kholia/DDX/Active-Antenna/Screenshot_2024-12-22_21-28-49.png

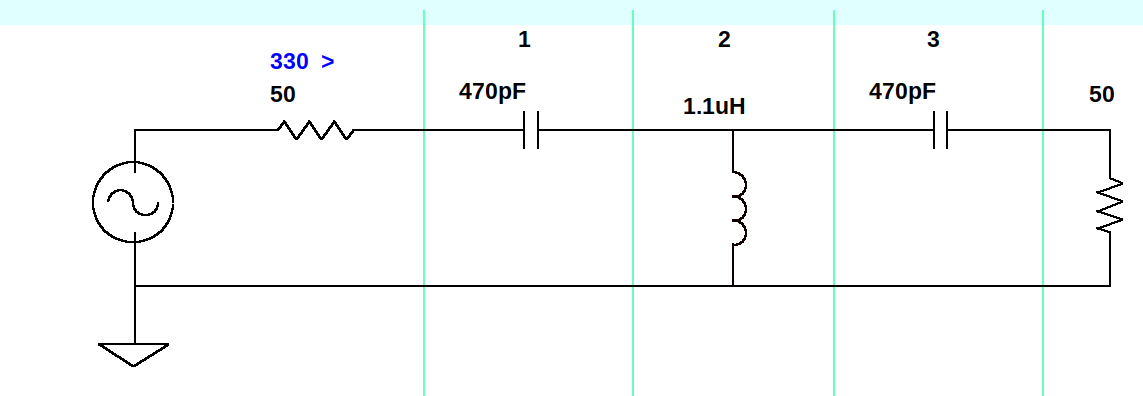
Active-Antenna/Screenshot_2024-12-22_21-28-49.png
