kholia/DDX/Active-Antenna/Screenshot_2024-12-22_21-56-25.png

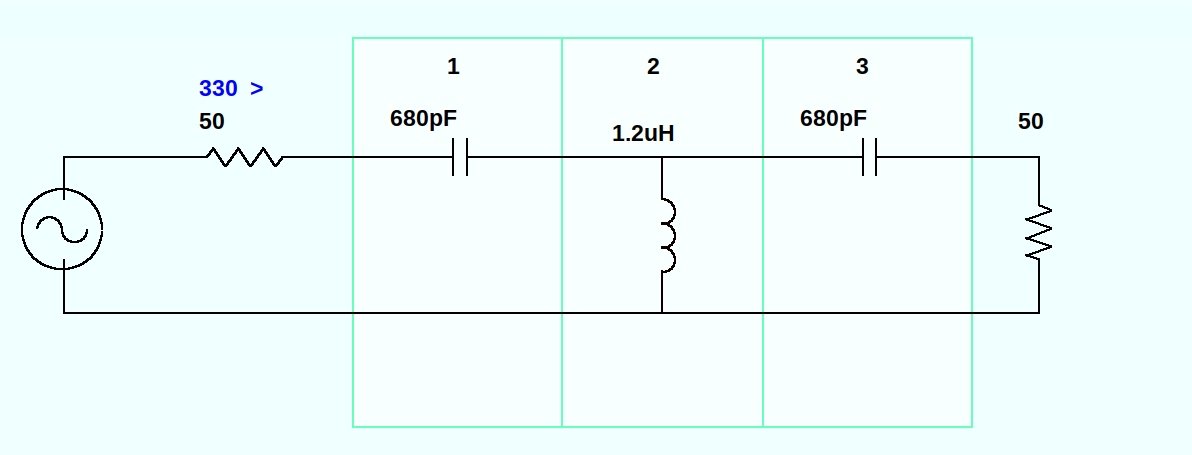
Active-Antenna/Screenshot_2024-12-22_21-56-25.png
