kholia/DDX/Active-Antenna/Screenshot_2024-12-23_18-33-32.png

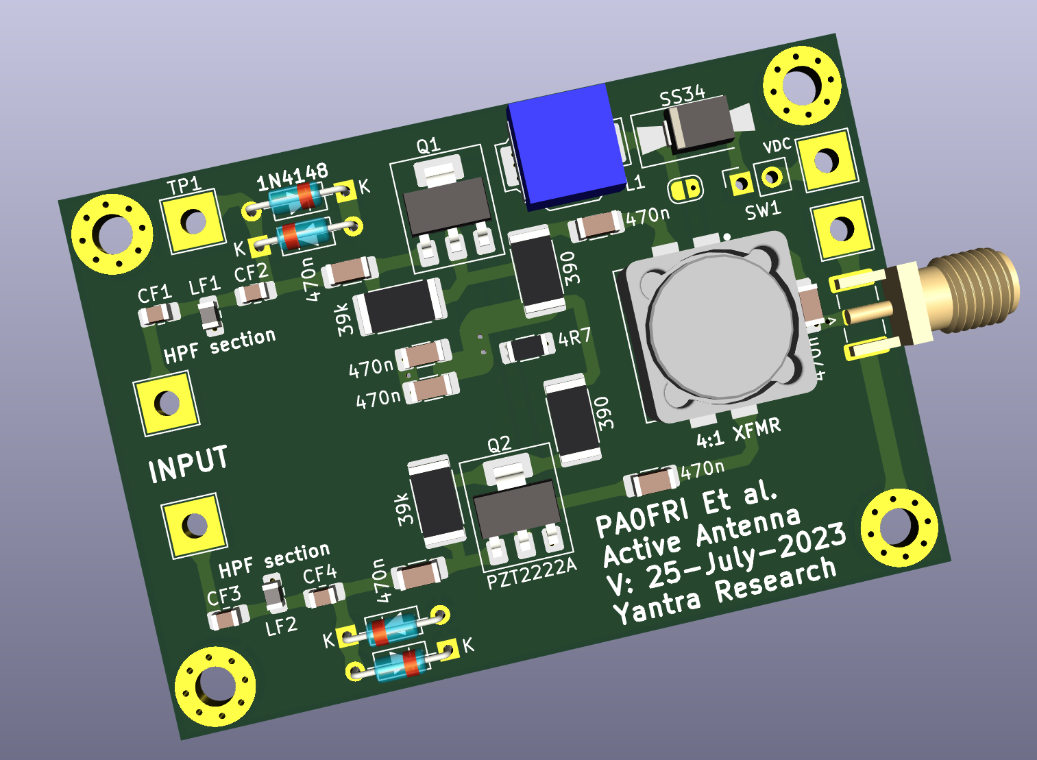
Active-Antenna/Screenshot_2024-12-23_18-33-32.png
