kholia/DDX/Active-Antenna/v 25-jul-2023.gif

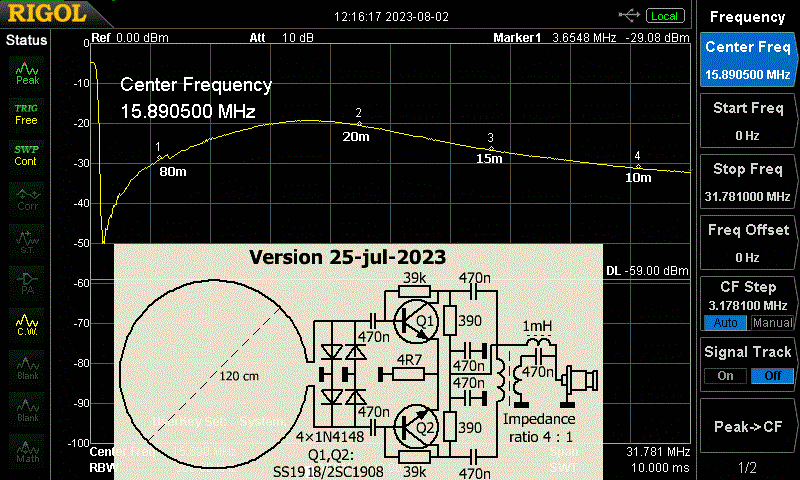
Active-Antenna/v 25-jul-2023.gif
