kholia/DDX/datasheets/8002-with-pot.jpg

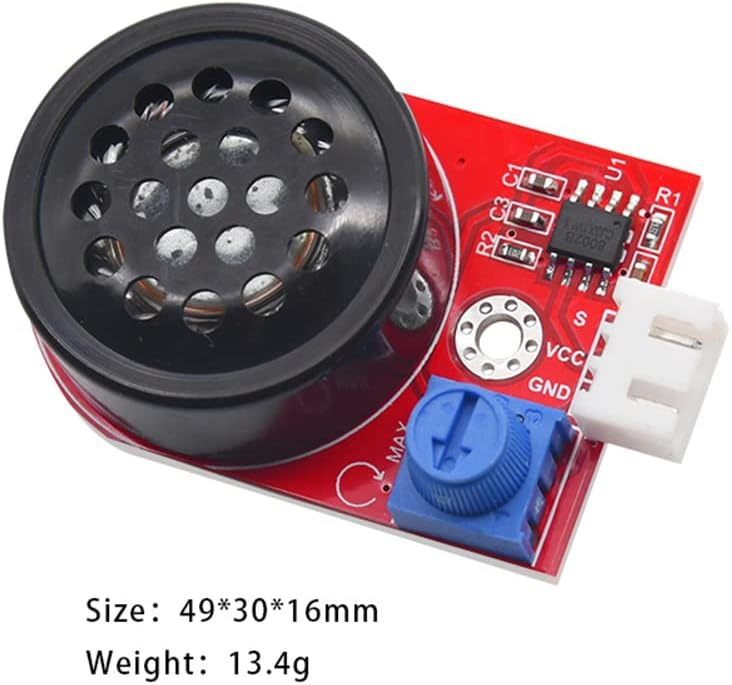
datasheets/8002-with-pot.jpg
