kholia/DDX/datasheets/CAPUF DC-DC LDO.png

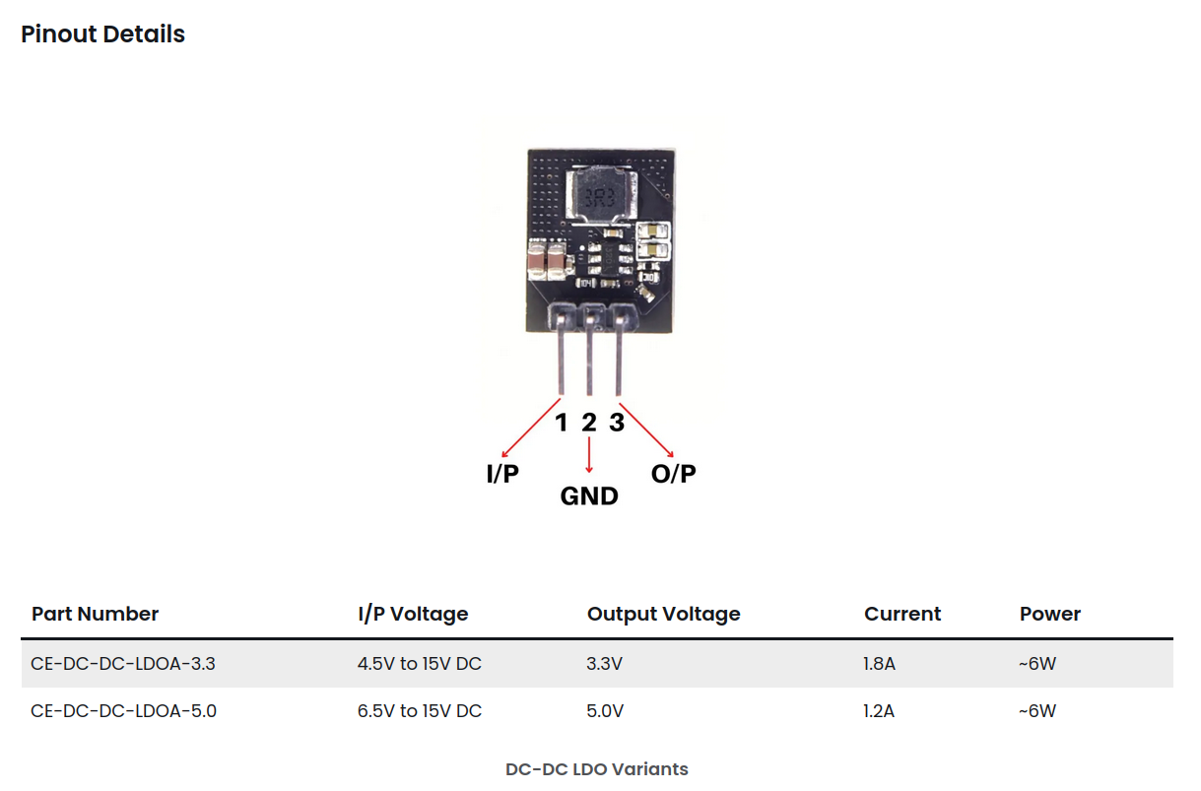
datasheets/CAPUF DC-DC LDO.png
