kholia/DDX/datasheets/Diode across relay.png

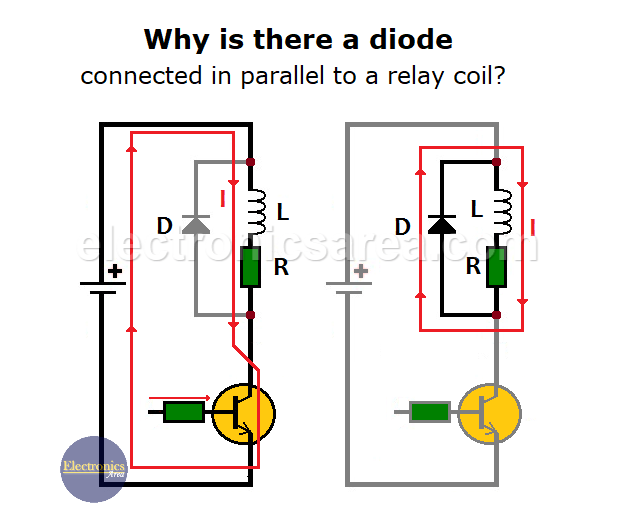
datasheets/Diode across relay.png
