kholia/DDX/datasheets/NeoPixel WS2812 LED - 5mm Diffused - THT.jpg

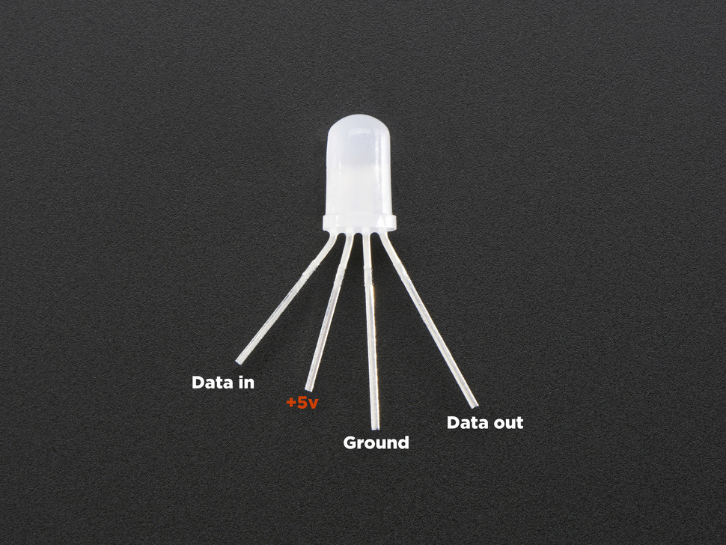
datasheets/NeoPixel WS2812 LED - 5mm Diffused - THT.jpg
