kholia/DDX/datasheets/Screenshot_2023-12-27_17-04-08.png

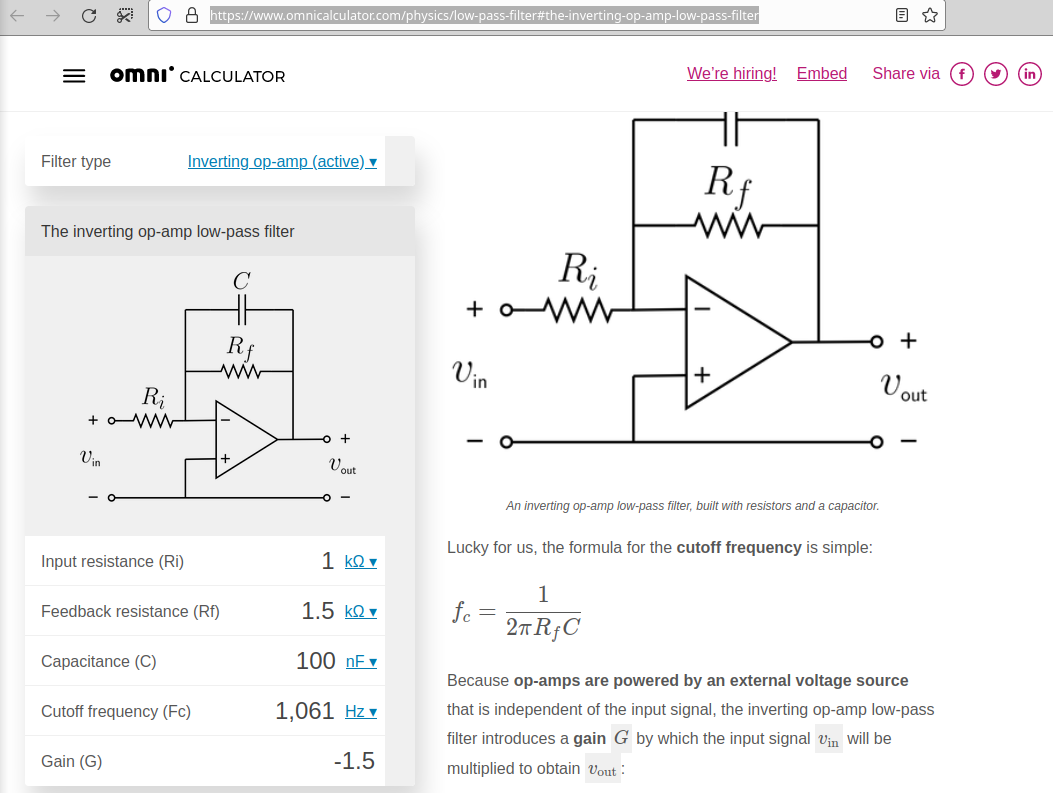
datasheets/Screenshot_2023-12-27_17-04-08.png
