kholia/DDX/datasheets/Screenshot_2024-01-10_11-48-58.png

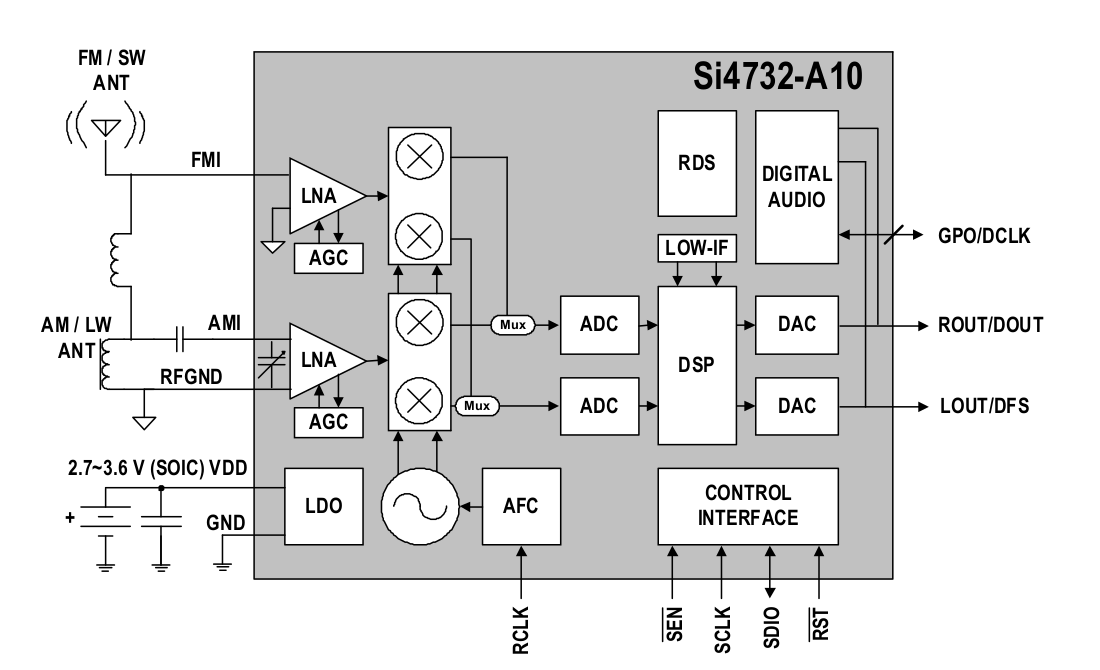
datasheets/Screenshot_2024-01-10_11-48-58.png
