kholia/DDX/datasheets/Screenshot_2024-05-21_07-38-28.png

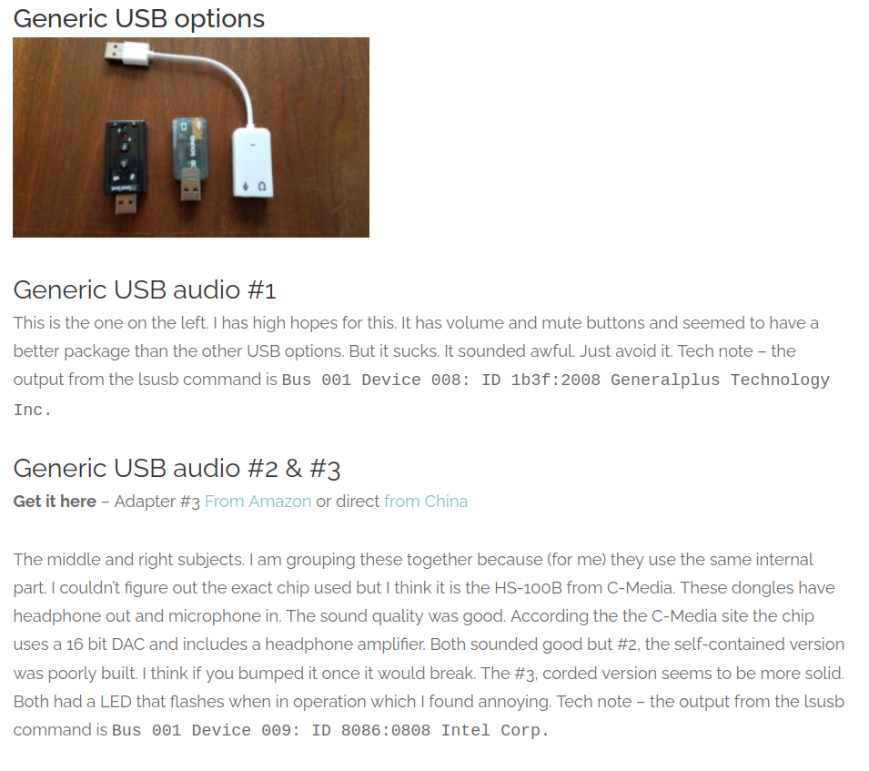
datasheets/Screenshot_2024-05-21_07-38-28.png
