kholia/DDX/datasheets/Screenshot_2024-05-21_07-54-50.png

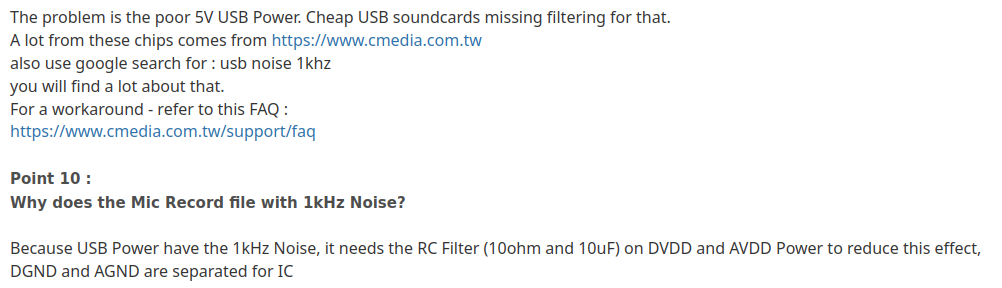
datasheets/Screenshot_2024-05-21_07-54-50.png
