kholia/DDX/datasheets/Screenshot_2024-10-01_17-50-52.png

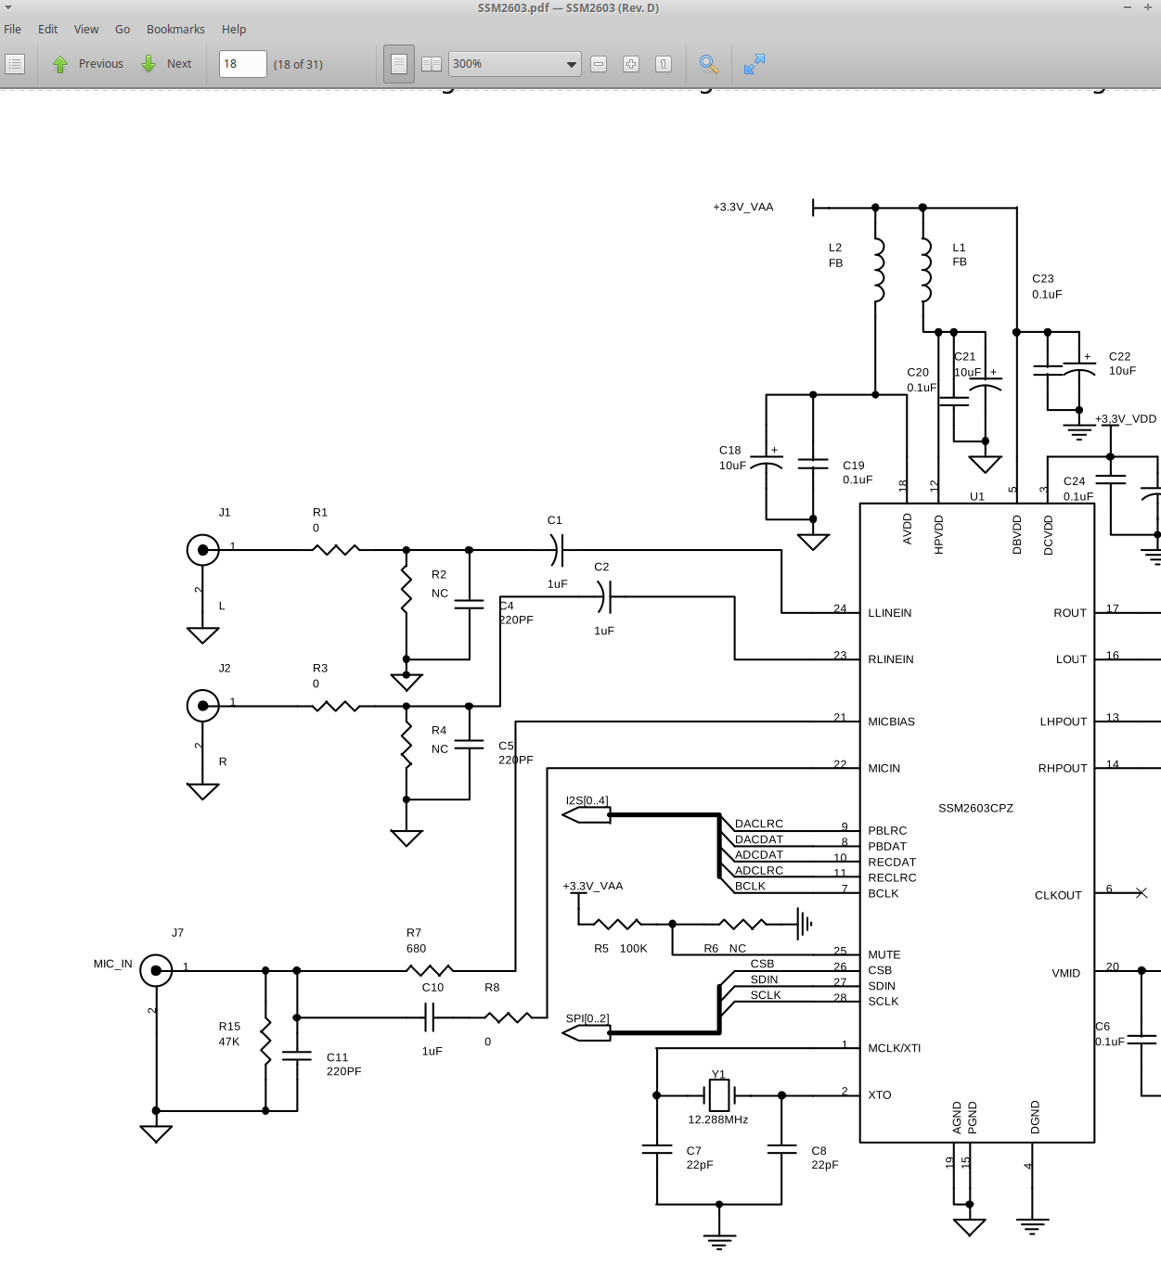
datasheets/Screenshot_2024-10-01_17-50-52.png
