kholia/DDX/datasheets/Screenshot_2024-10-03_21-19-48.png

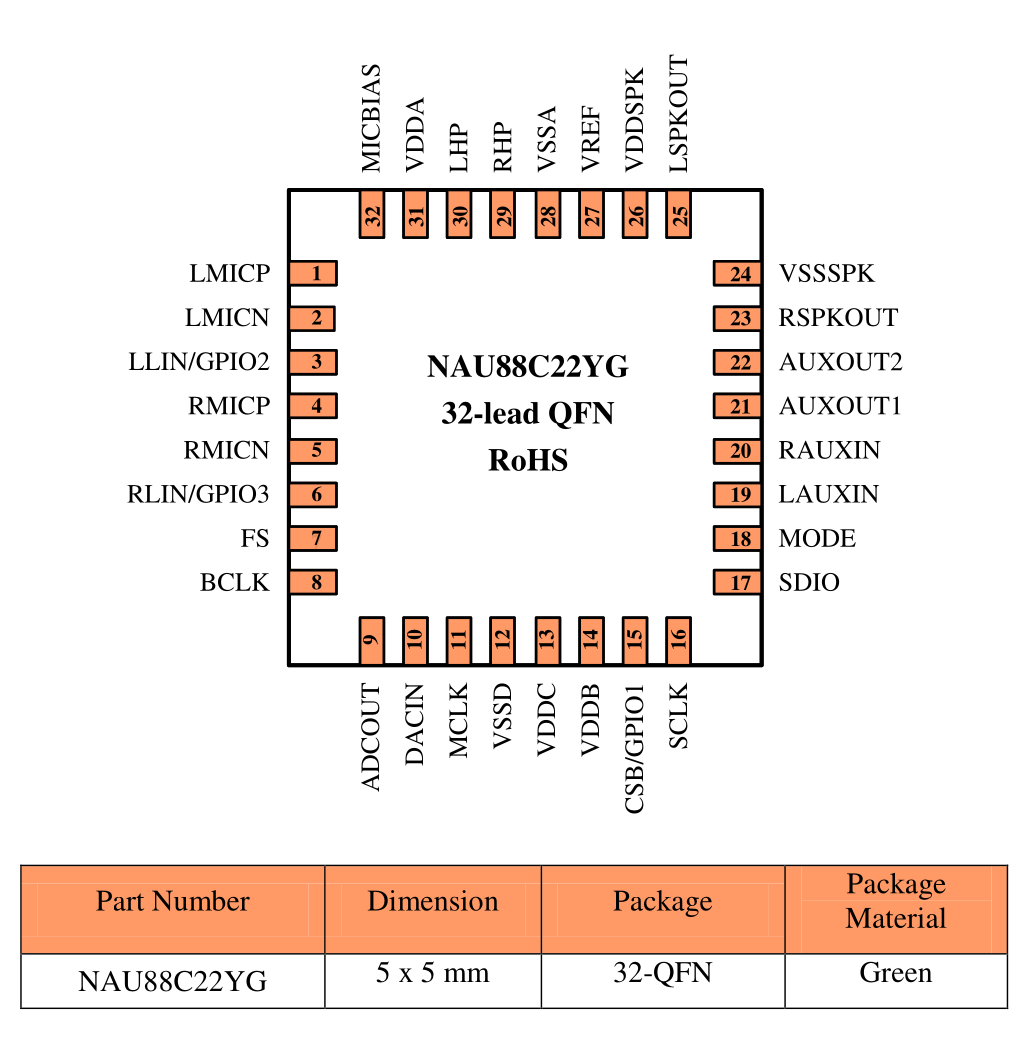
datasheets/Screenshot_2024-10-03_21-19-48.png
