kholia/DDX/datasheets/Screenshot_2024-10-03_21-23-47.png

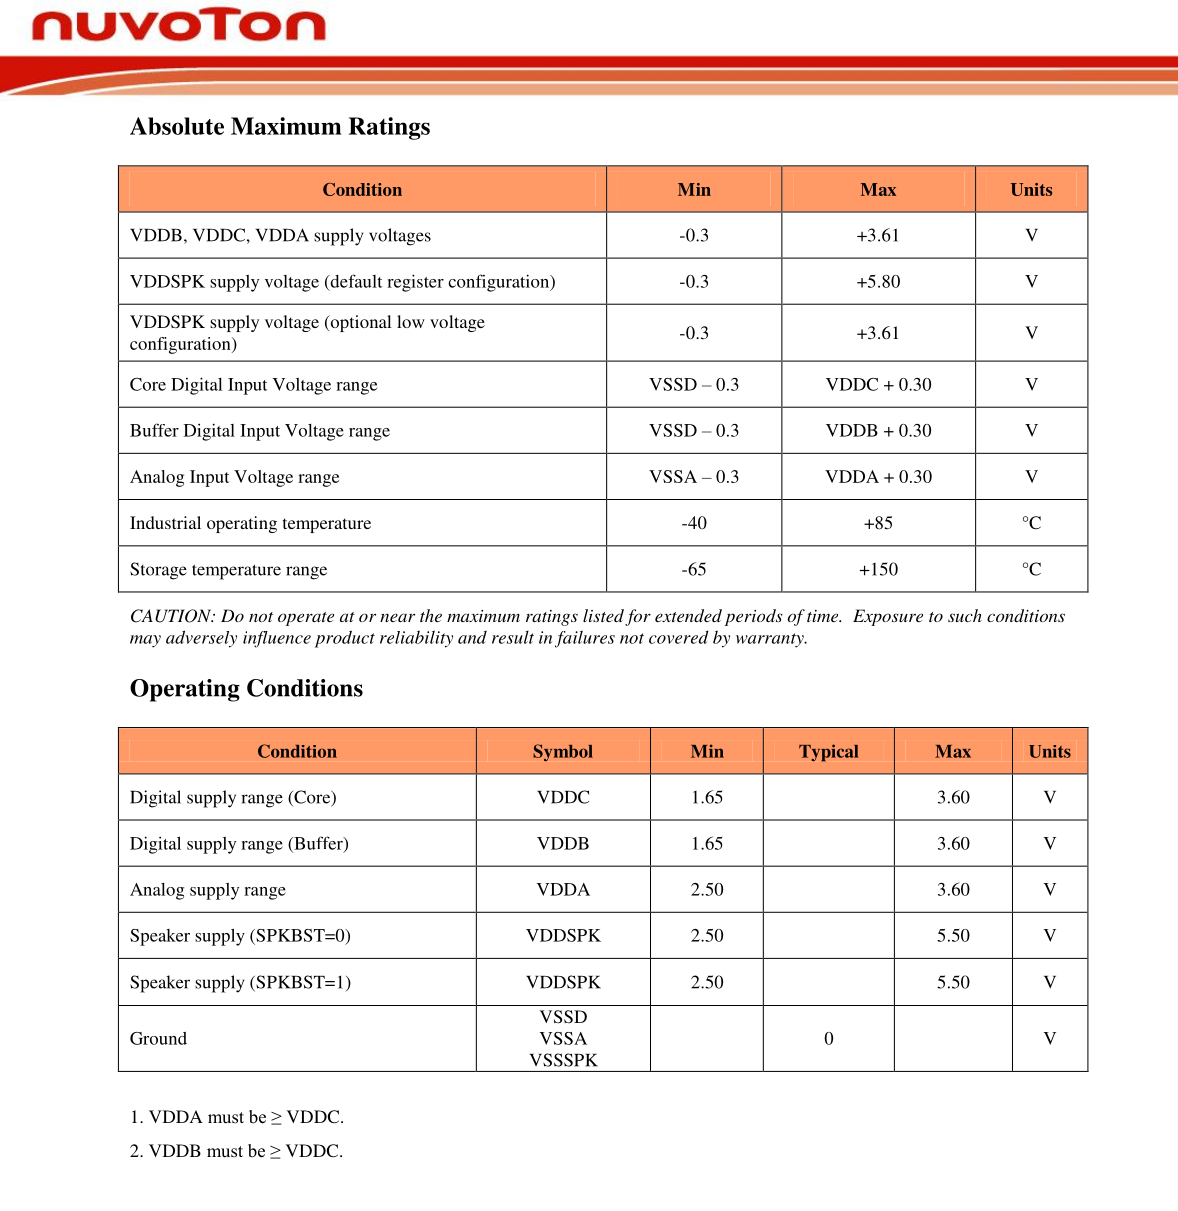
datasheets/Screenshot_2024-10-03_21-23-47.png
