kholia/DDX/datasheets/SFU455B Pinout.png

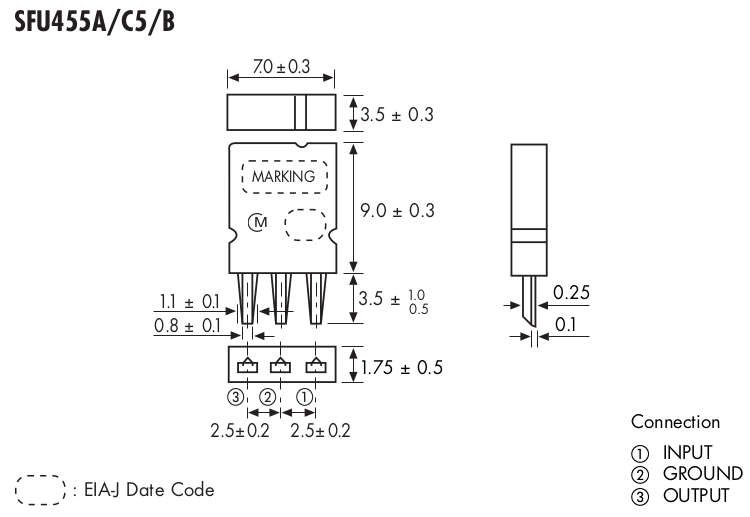
datasheets/SFU455B Pinout.png
