kholia/DDX/datasheets/speaker-for-micro-bit-1-500x500.jpg

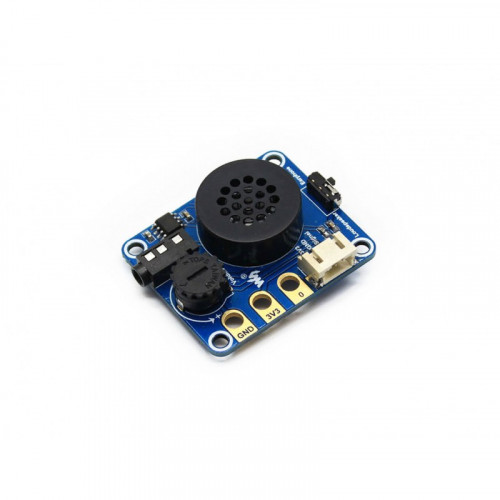
datasheets/speaker-for-micro-bit-1-500x500.jpg
