kholia/DDX/DDX-1-R1.10/3D-Render.png

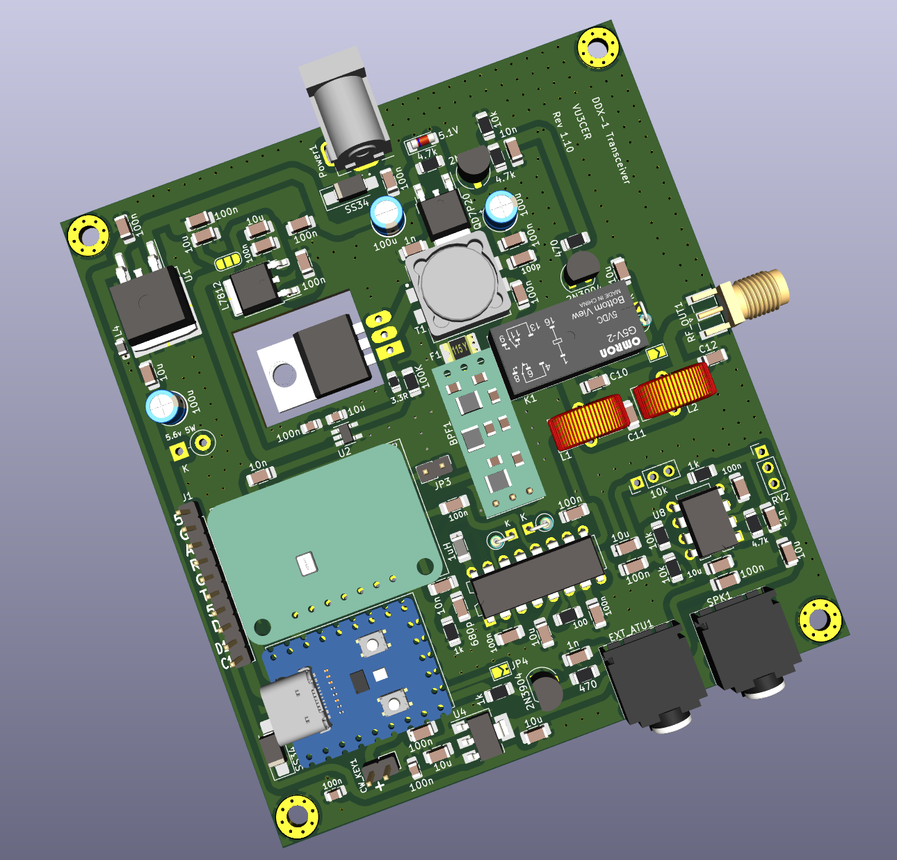
DDX-1-R1.10/3D-Render.png
