kholia/DDX/DDX-1-R1.10/Screenshot_2023-11-16_10-58-44.png

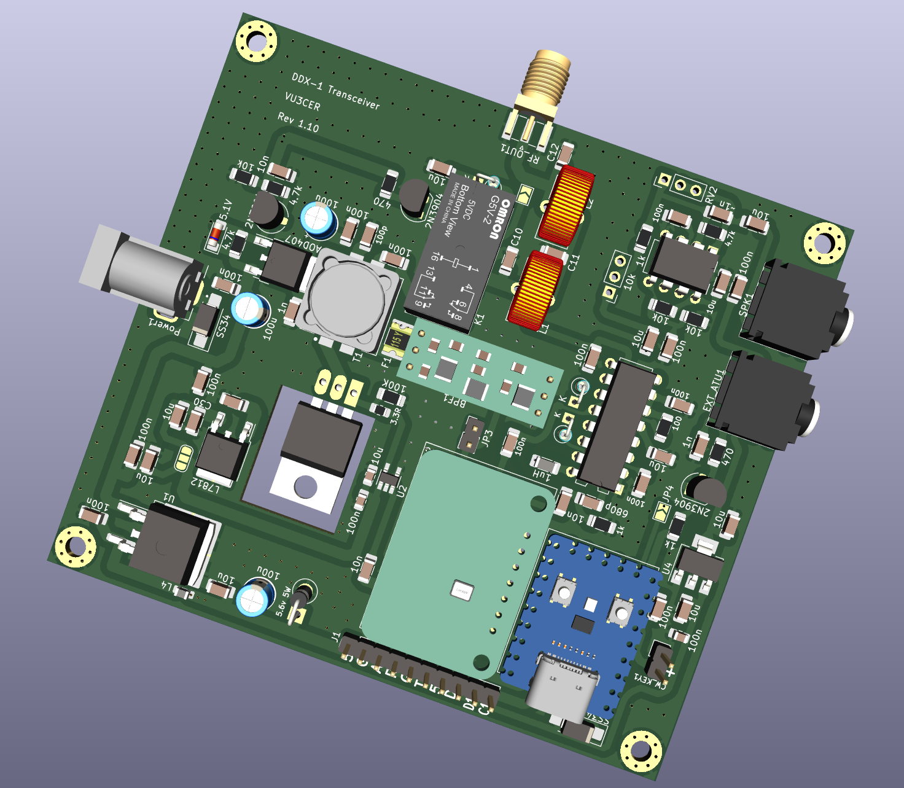
DDX-1-R1.10/Screenshot_2023-11-16_10-58-44.png
