kholia/DDX/DDX-1-R1.10/Screenshot_2024-07-12_11-12-55.png

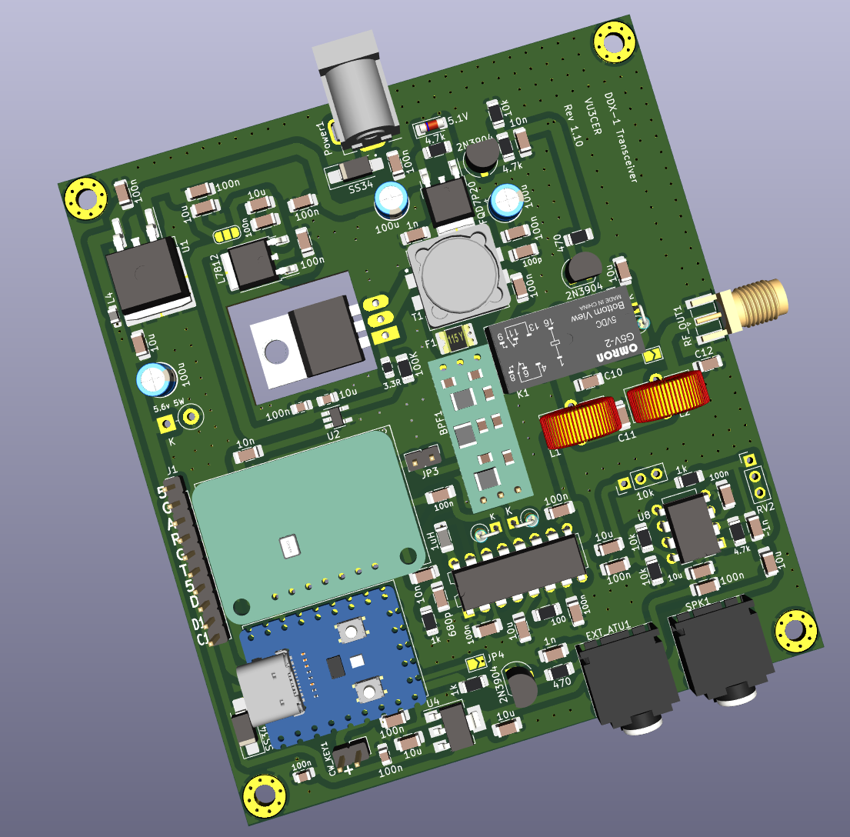
DDX-1-R1.10/Screenshot_2024-07-12_11-12-55.png
