kholia/DDX/Pictures/IMG_20231203_173641.jpg

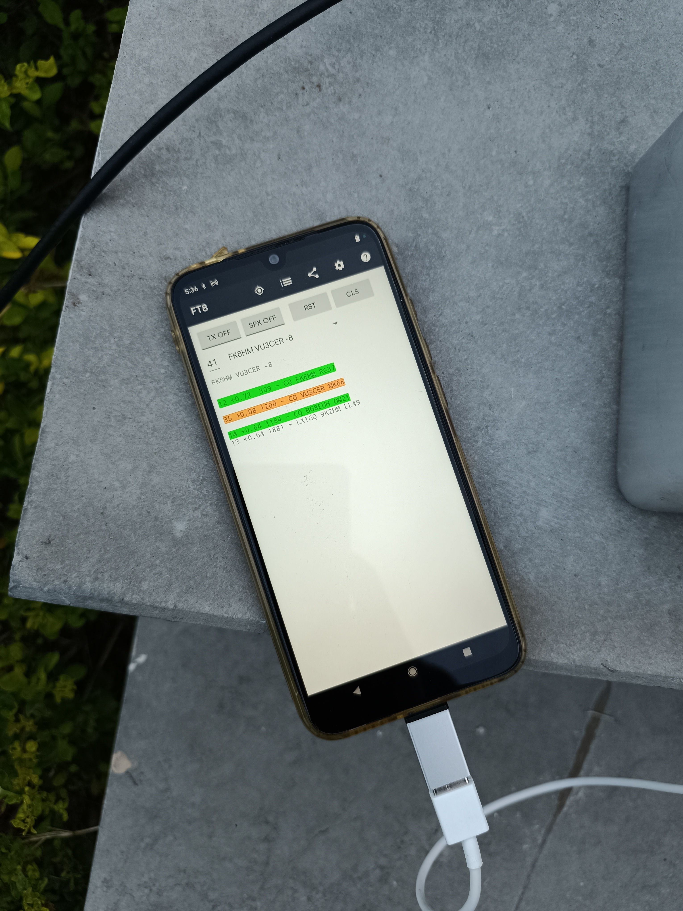
Pictures/IMG_20231203_173641.jpg
