kholia/DDX/Pictures/IMG_20231222_163501.jpg

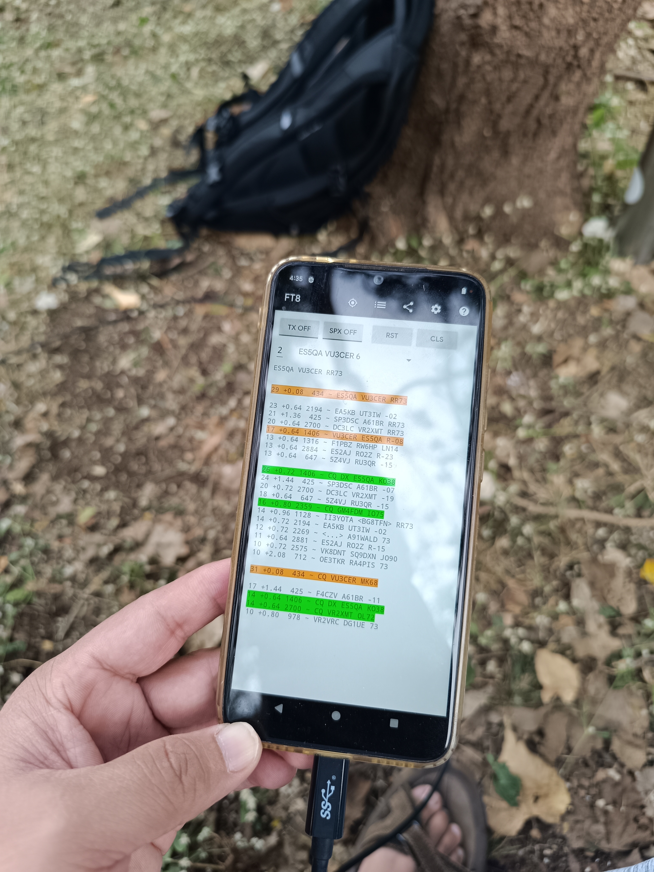
Pictures/IMG_20231222_163501.jpg
