kholia/DDX/Pictures/IMG_20231222_163504.jpg

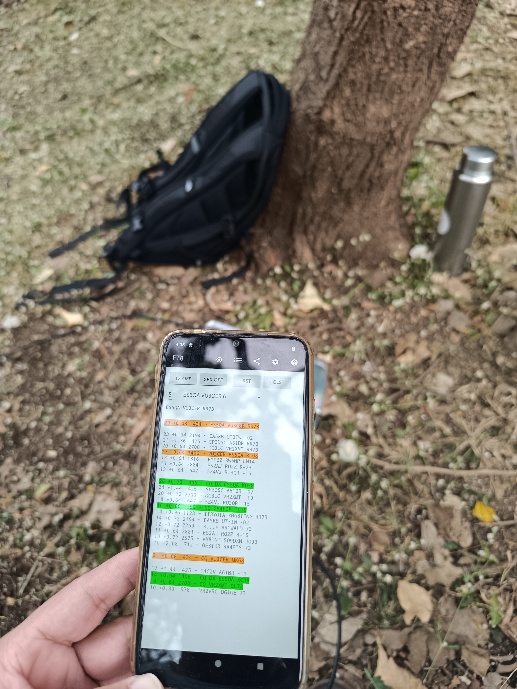
Pictures/IMG_20231222_163504.jpg
