kholia/DDX/Pictures/IMG_20231225_163345.jpg

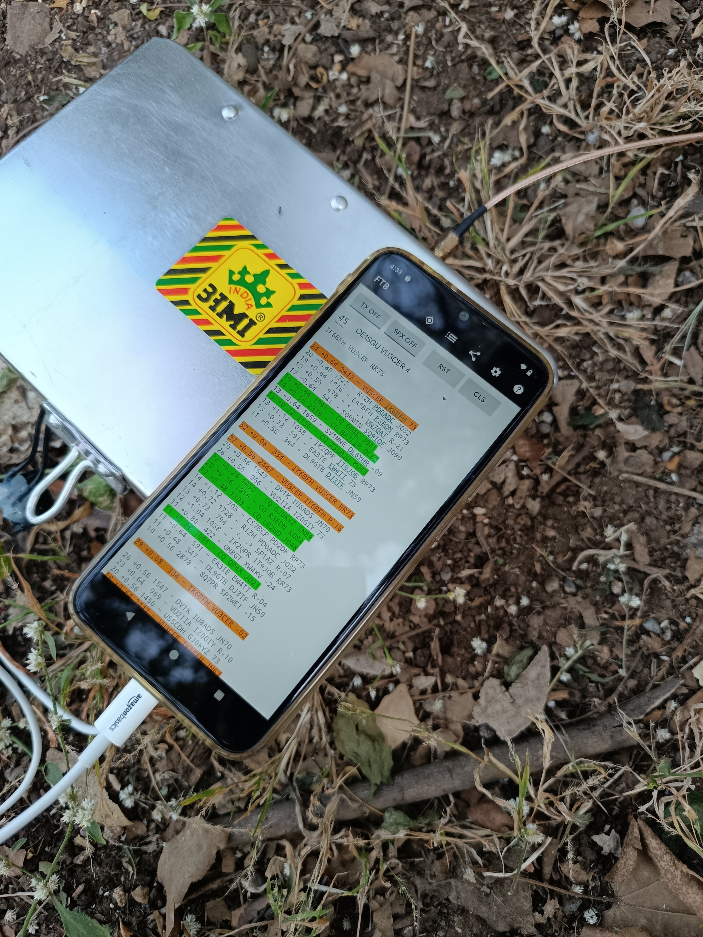
Pictures/IMG_20231225_163345.jpg
