kholia/DDX/Pictures/IMG_20231225_171434.jpg

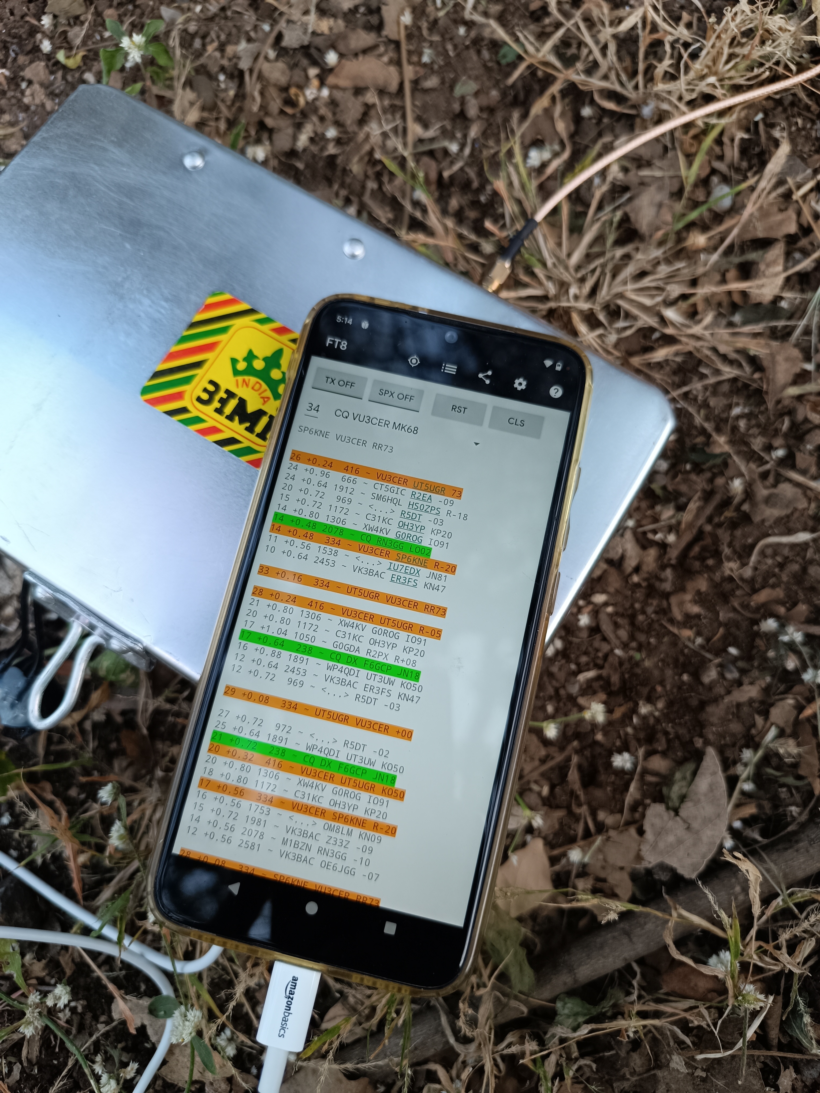
Pictures/IMG_20231225_171434.jpg
