kholia/DDX/Pictures/picture_reduced.png

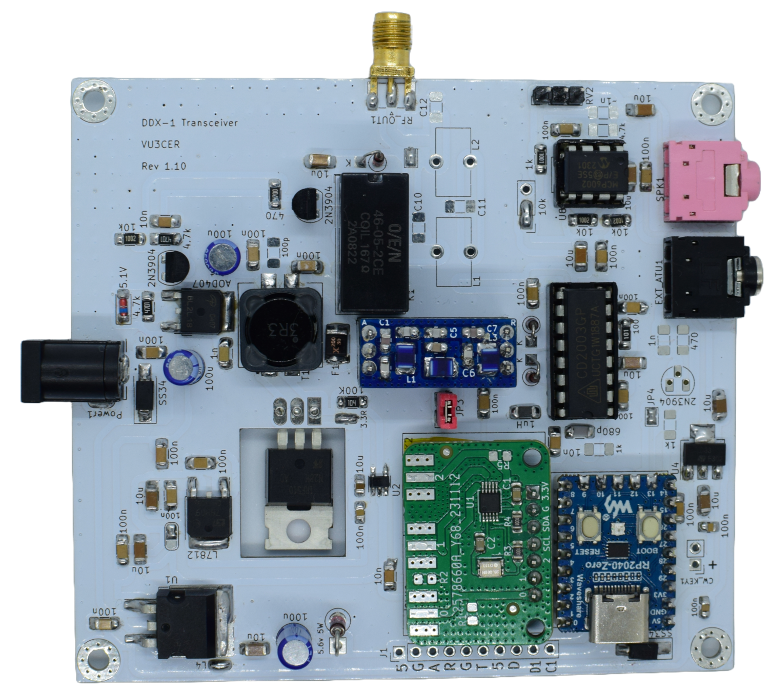
Pictures/picture_reduced.png
