kholia/DDX/Pictures/smaller_with_hs.png

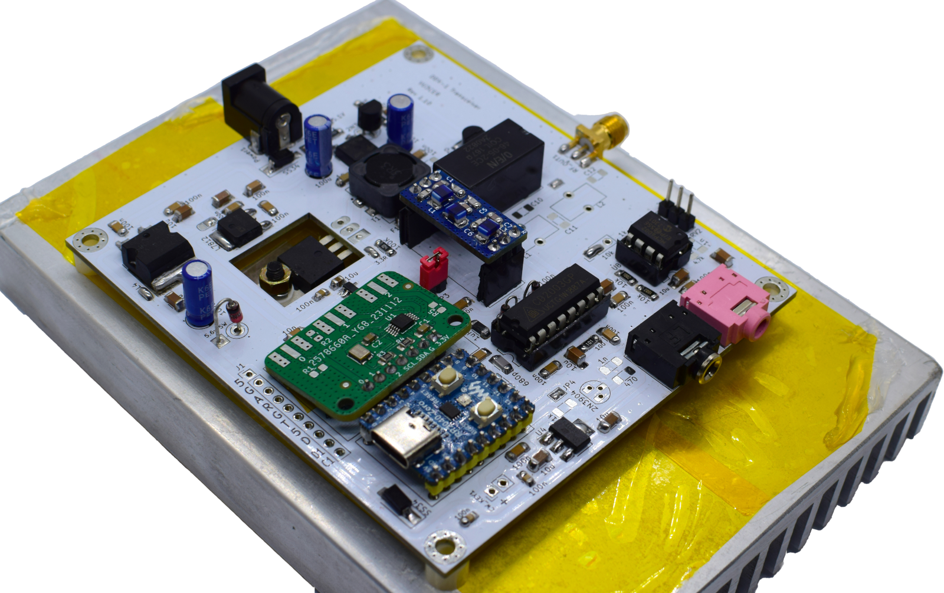
Pictures/smaller_with_hs.png
