kholia/DDX/RX-TX-BPF-2025-v2/14M-Screenshot_2024-12-20_16-44-34.png

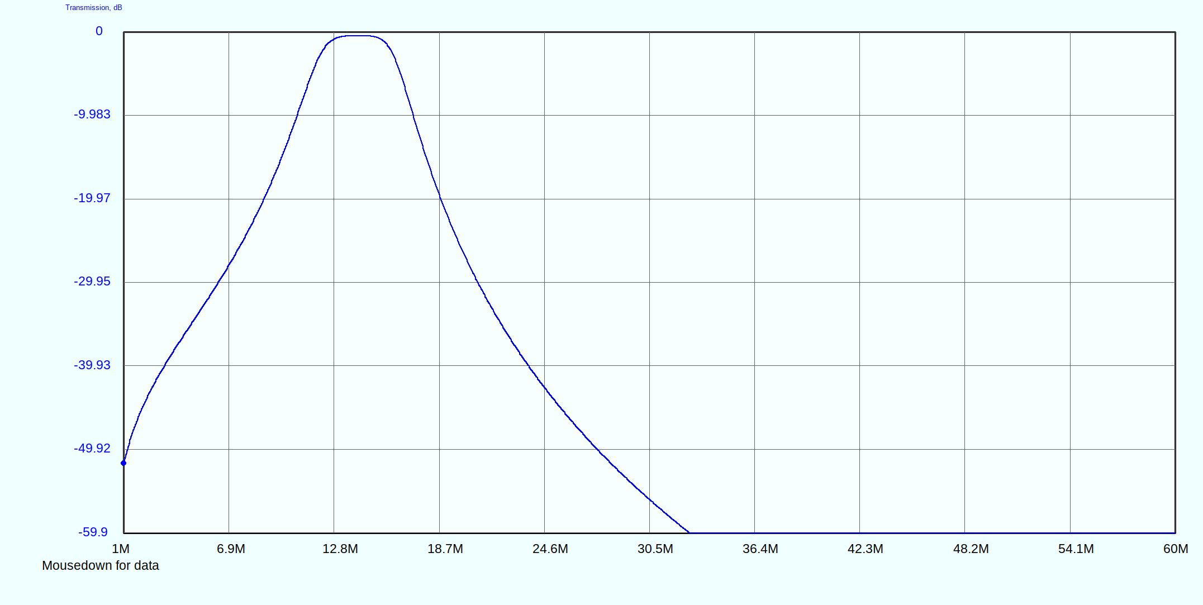
RX-TX-BPF-2025-v2/14M-Screenshot_2024-12-20_16-44-34.png
