kholia/DDX/RX-TX-BPF-2025-v2/28M-Screenshot_2024-12-19_19-49-46.png

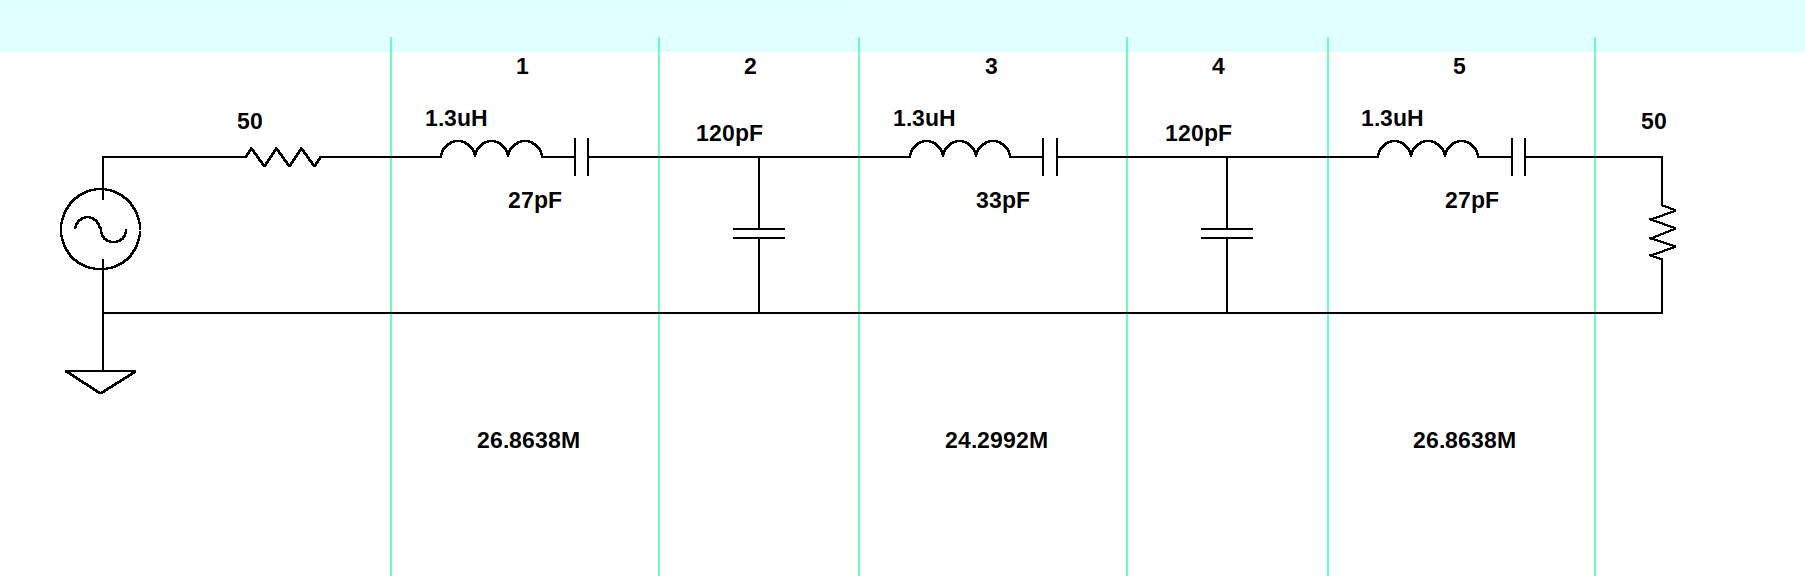
RX-TX-BPF-2025-v2/28M-Screenshot_2024-12-19_19-49-46.png
