kholia/DDX/RX-TX-BPF-2025-v2/Modeling-Actual-Values-28-MHz/Screenshot_2024-12-20_11-46-58.png

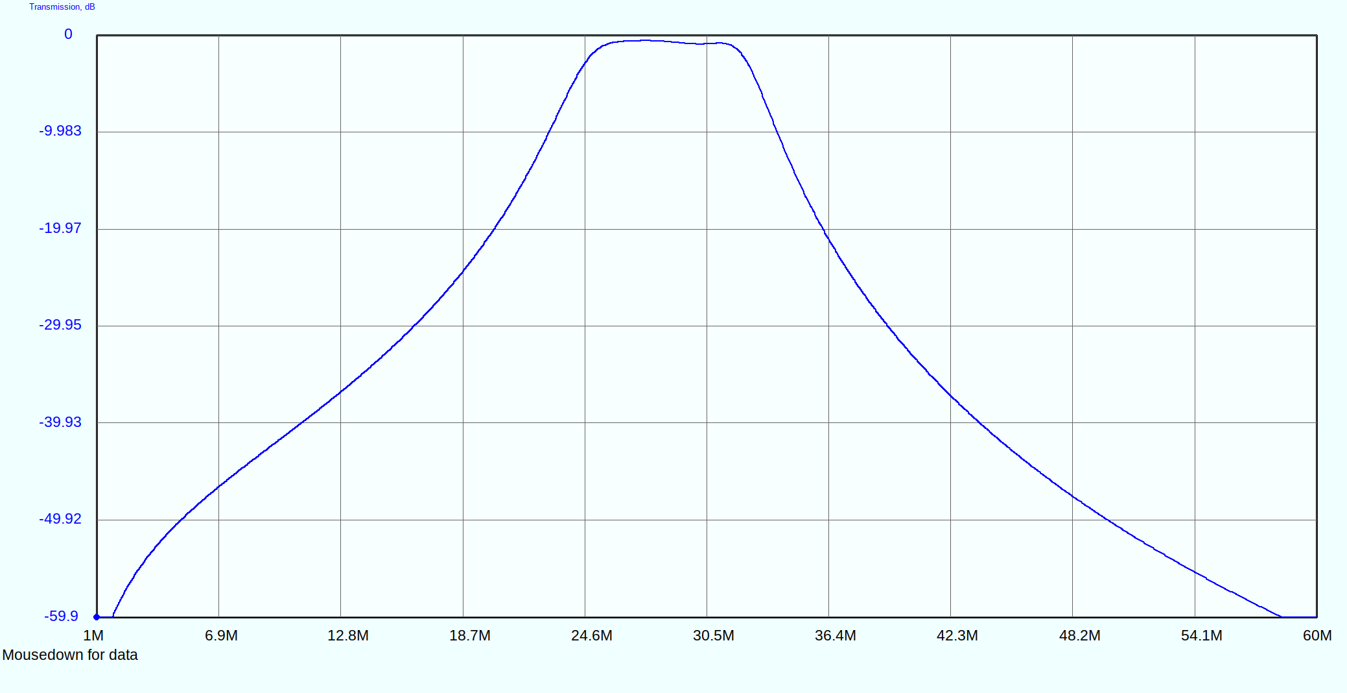
RX-TX-BPF-2025-v2/Modeling-Actual-Values-28-MHz/Screenshot_2024-12-20_11-46-58.png
