kholia/DDX/RX-TX-BPF-2025-v2/pft-practical.png

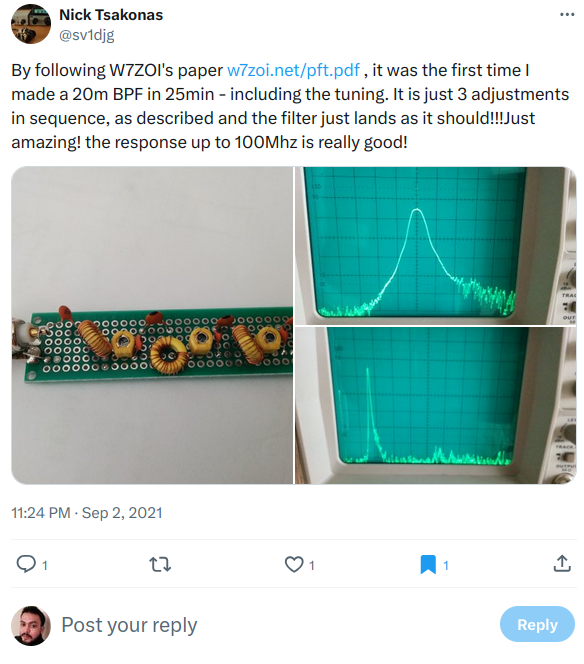
RX-TX-BPF-2025-v2/pft-practical.png
