kholia/DDX/RX-TX-BPF-2025-v2/Screenshot_2024-12-20_12-20-08.png

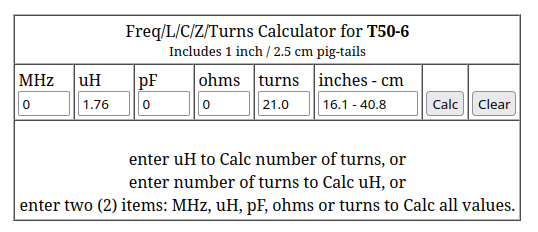
RX-TX-BPF-2025-v2/Screenshot_2024-12-20_12-20-08.png
