kholia/DDX/RX-TX-BPF-2025-v2/Screenshot_2024-12-23_11-25-25.png

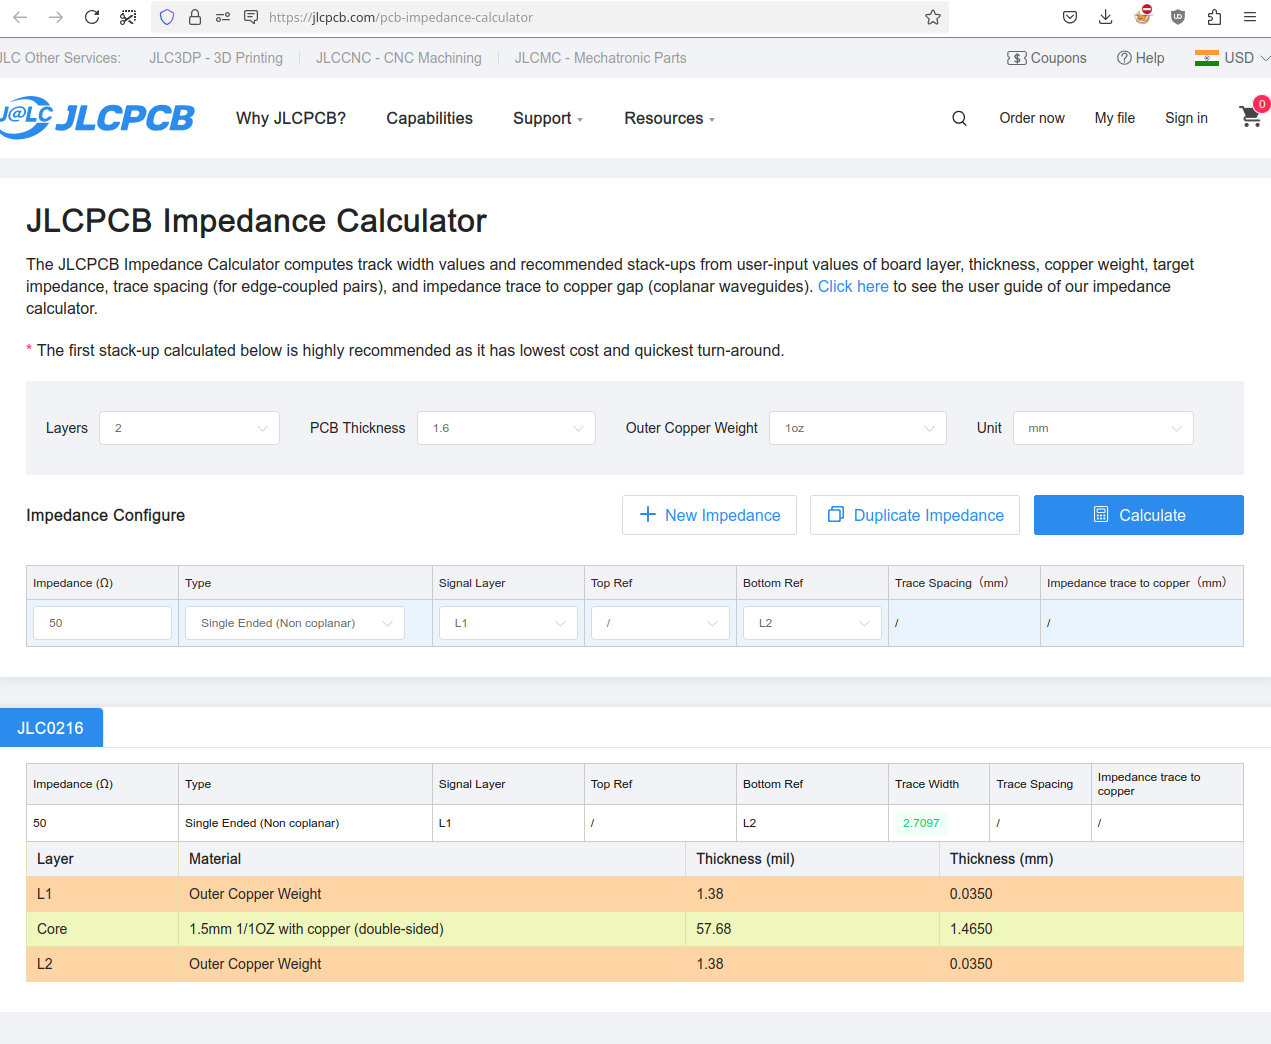
RX-TX-BPF-2025-v2/Screenshot_2024-12-23_11-25-25.png
