kholia/DDX/screenshots/DDX-Commercial-3.png

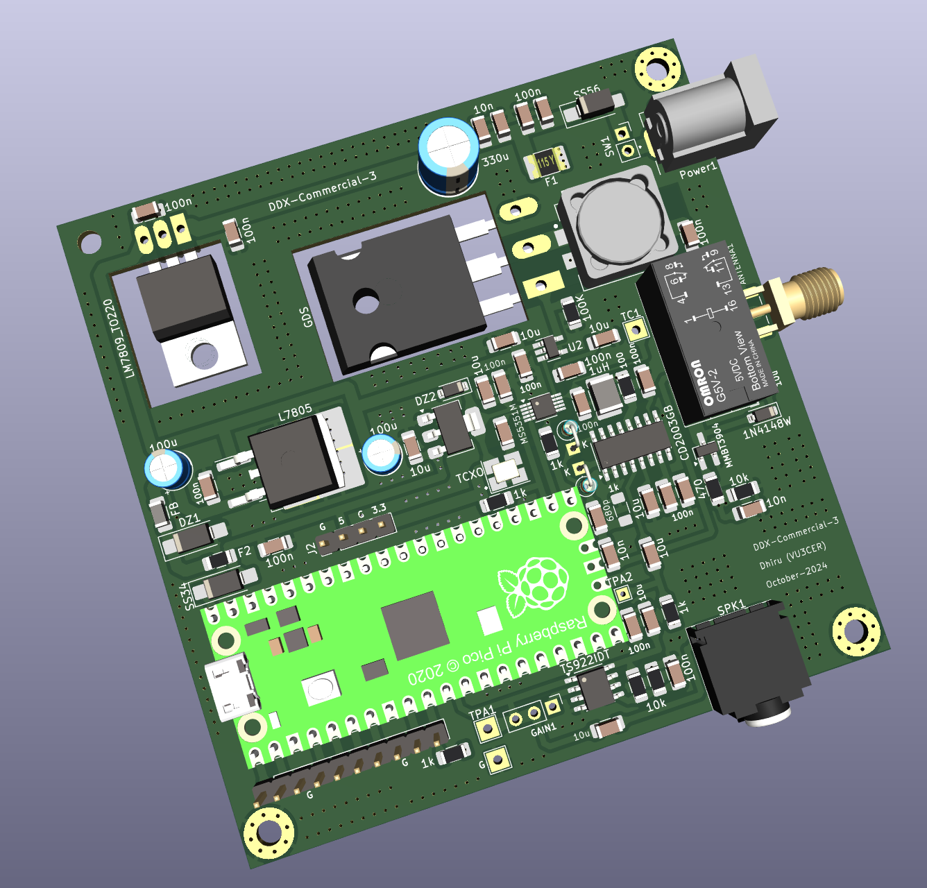
screenshots/DDX-Commercial-3.png
