kholia/DDX/screenshots/JLCPCBA-1.png

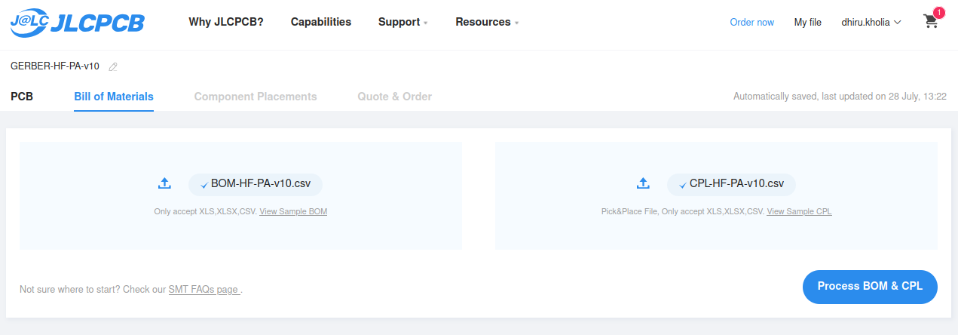
screenshots/JLCPCBA-1.png
