kholia/DDX/screenshots/JLCPCBA-2.png

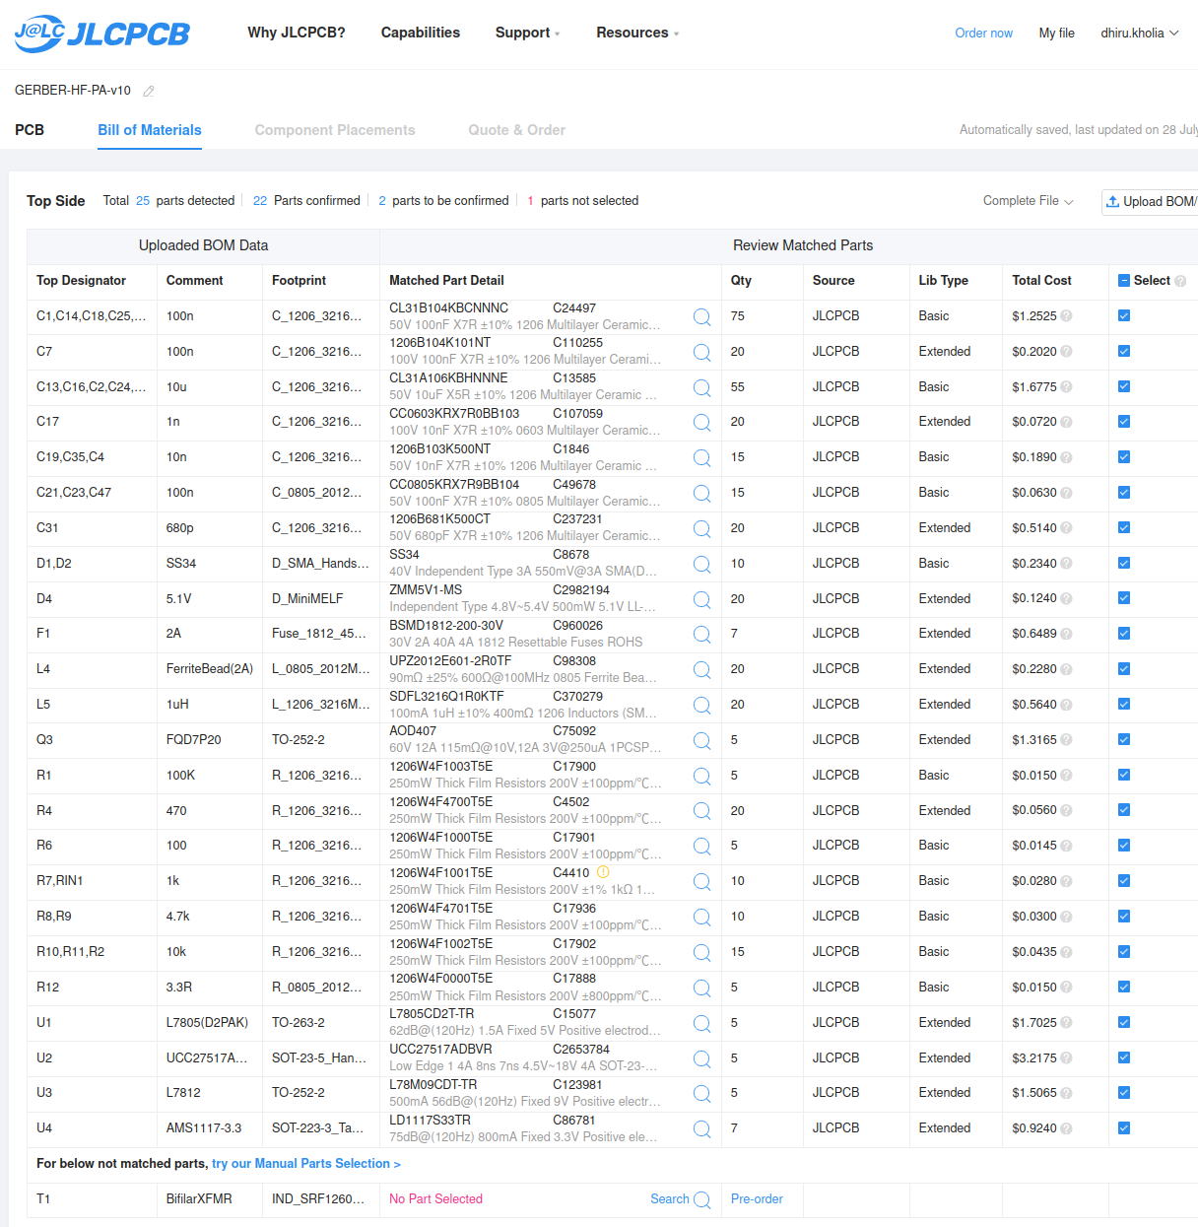
screenshots/JLCPCBA-2.png
