kholia/DDX/screenshots/JLCPCBA-3.png

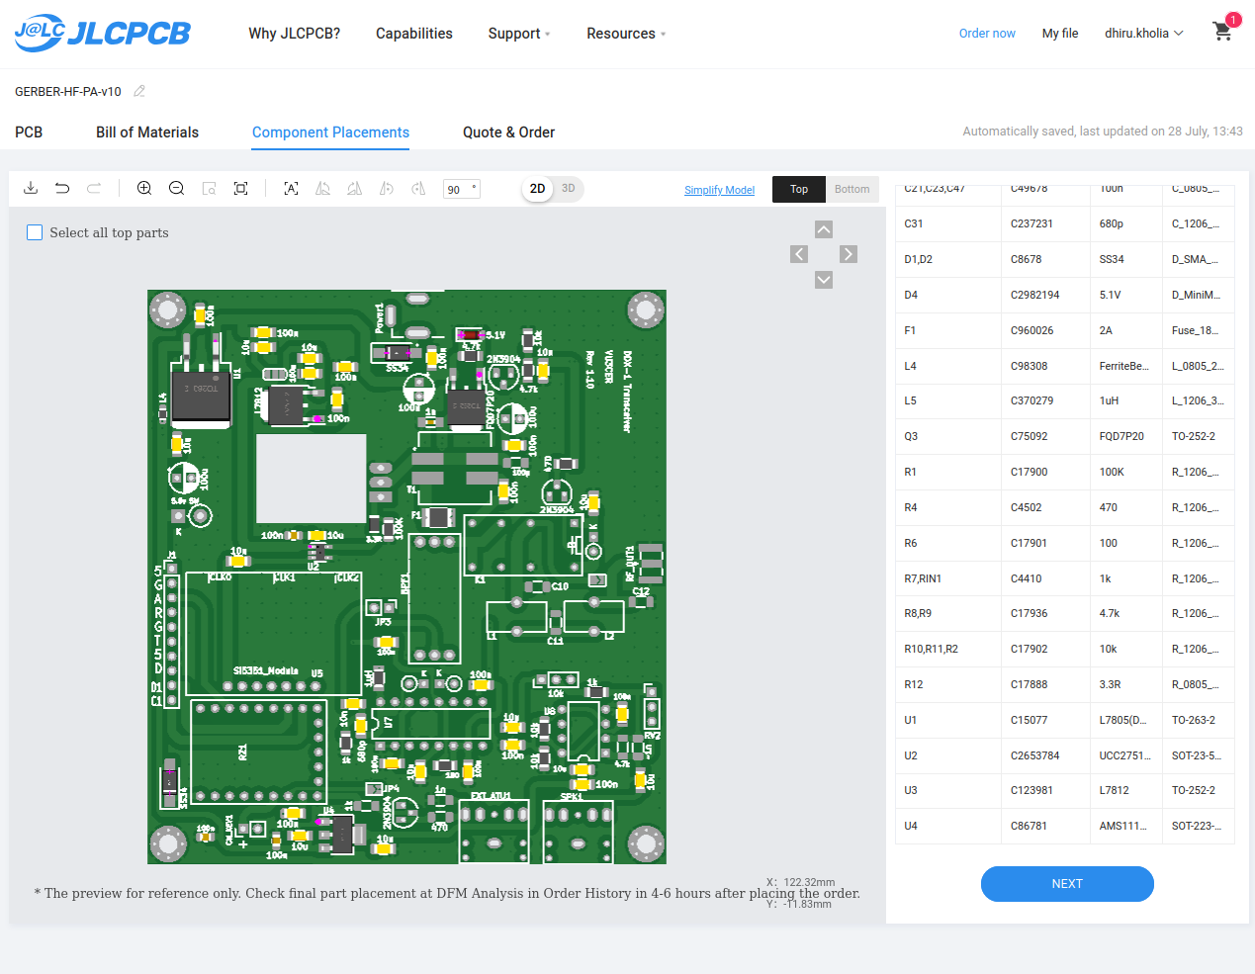
screenshots/JLCPCBA-3.png
