kholia/DDX/screenshots/Pico-ADC-Screenshot_2023-11-22_13-48-06.png

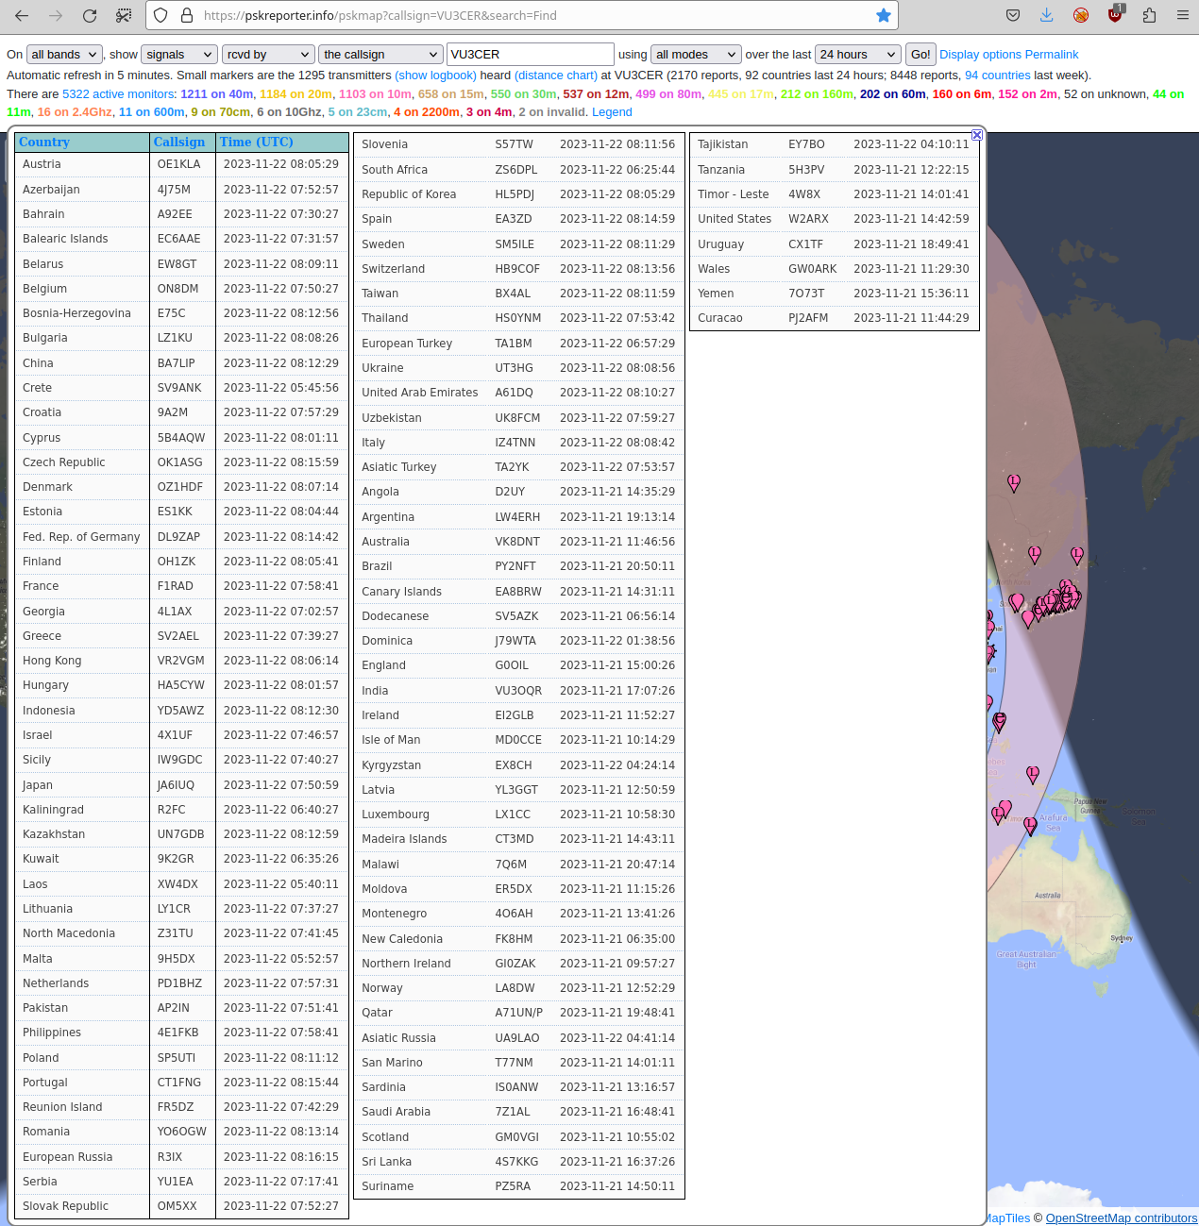
screenshots/Pico-ADC-Screenshot_2023-11-22_13-48-06.png
