kholia/DDX/screenshots/RX-Screenshot_2023-11-30_20-05-11.png

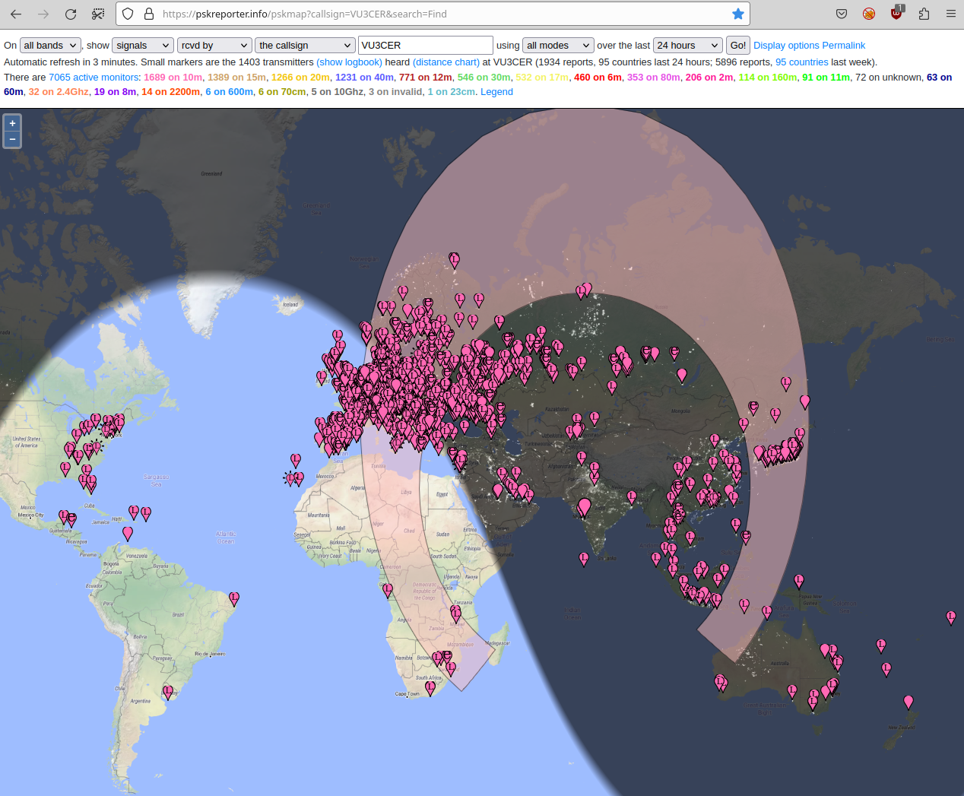
screenshots/RX-Screenshot_2023-11-30_20-05-11.png
