kholia/DDX/screenshots/RX-Screenshot_2023-11-30_21-44-51.png

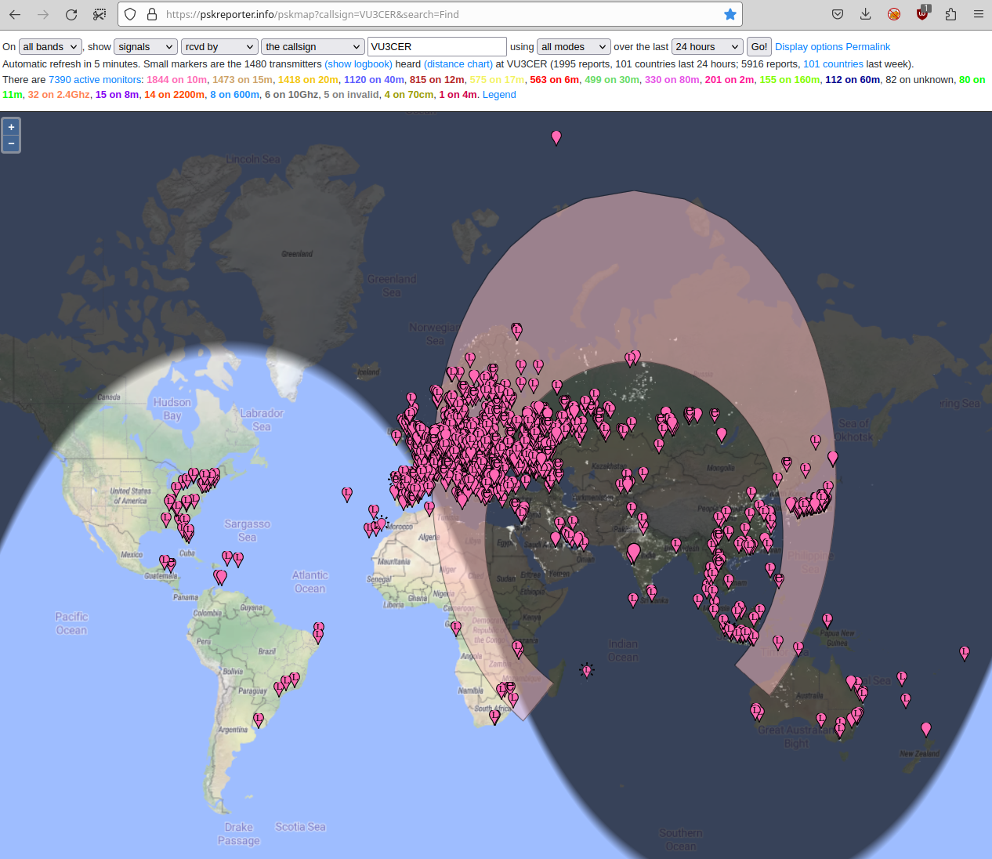
screenshots/RX-Screenshot_2023-11-30_21-44-51.png
