kholia/DDX/screenshots/San-Merino-QSO.png

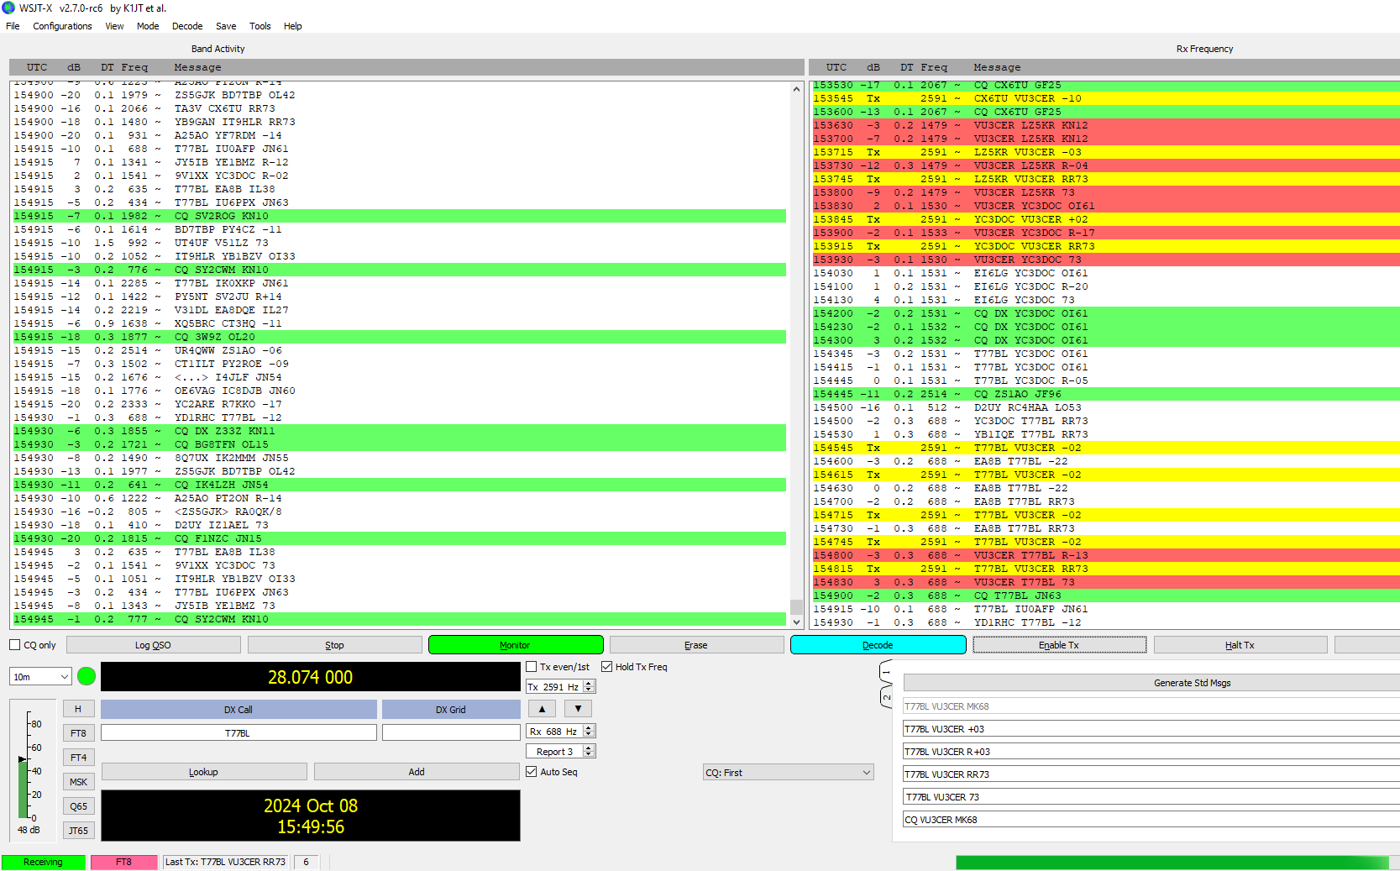
screenshots/San-Merino-QSO.png
