kholia/DDX/screenshots/Screenshot_2023-11-17_19-35-13.png

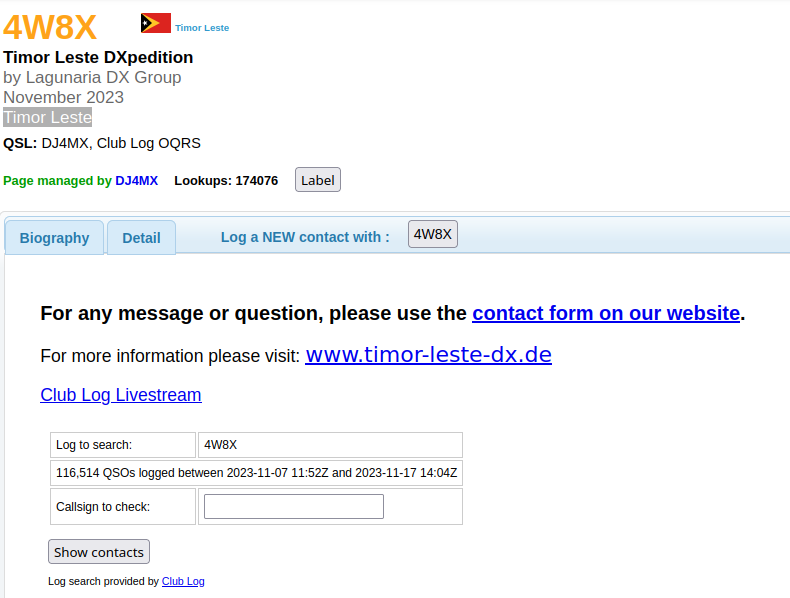
screenshots/Screenshot_2023-11-17_19-35-13.png
