kholia/DDX/screenshots/Screenshot_2023-11-17_19-37-47.png

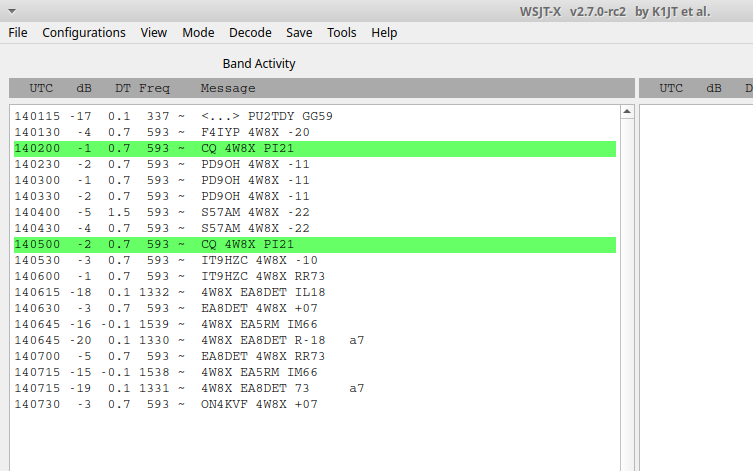
screenshots/Screenshot_2023-11-17_19-37-47.png
