kholia/DDX/screenshots/Screenshot_2023-11-24_19-33-11.png

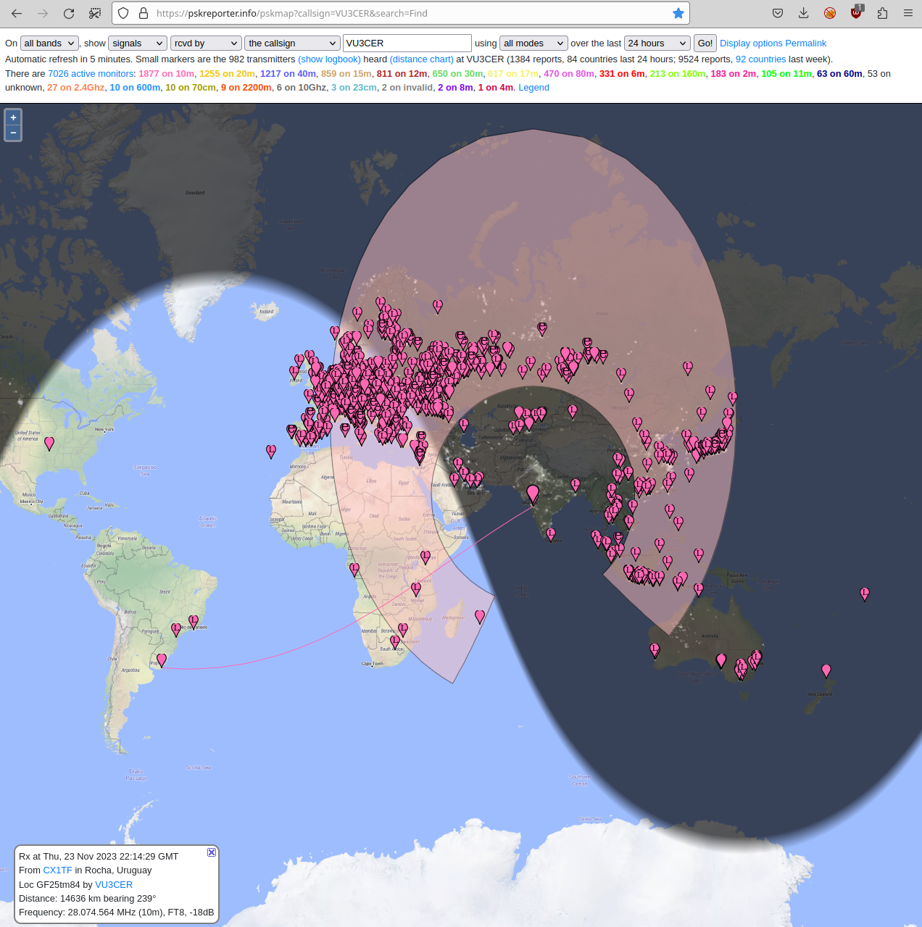
screenshots/Screenshot_2023-11-24_19-33-11.png
