kholia/DDX/screenshots/Screenshot_2024-03-21_10-22-18.png

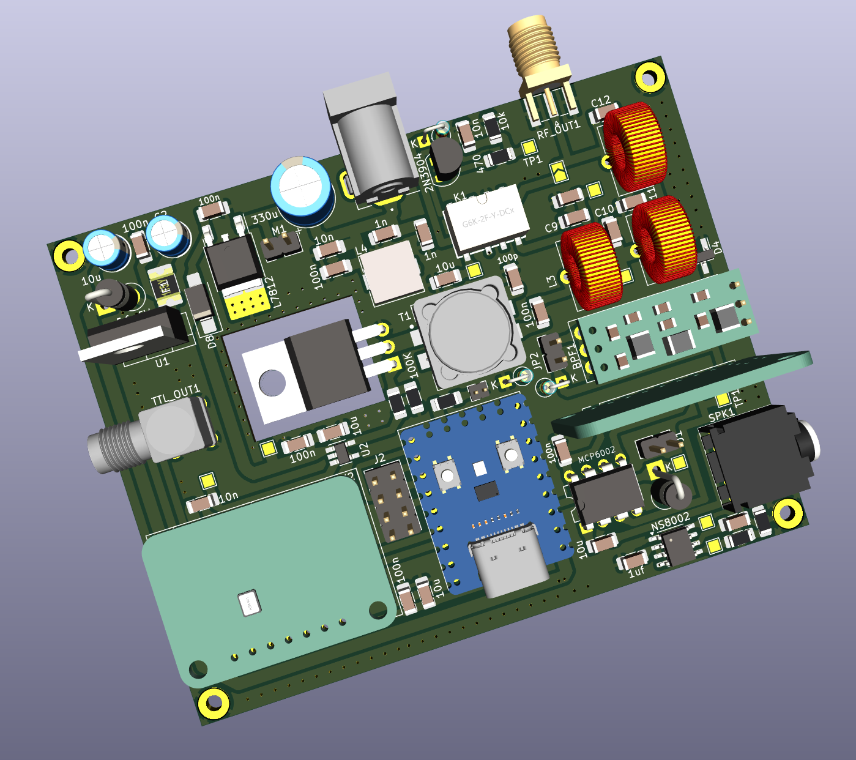
screenshots/Screenshot_2024-03-21_10-22-18.png
