kholia/DDX/screenshots/Screenshot_2024-10-01_16-03-29.png

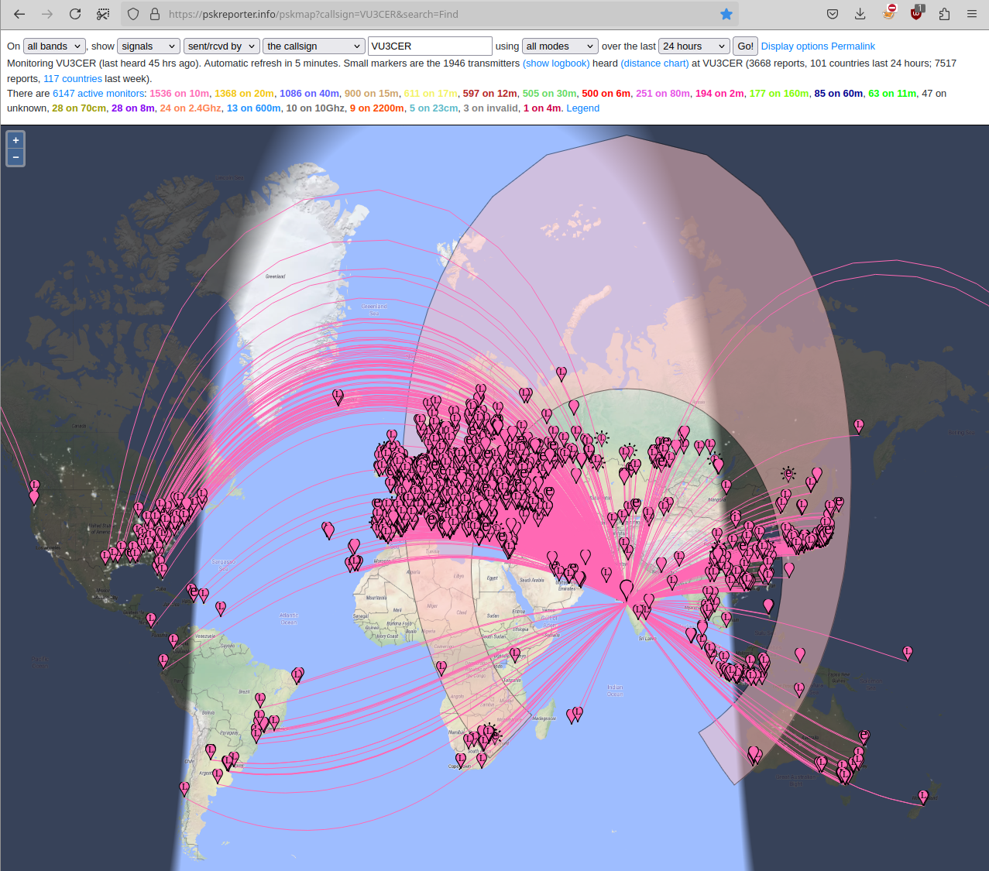
screenshots/Screenshot_2024-10-01_16-03-29.png
