kholia/DDX/screenshots/Screenshot_2024-10-03_06-31-26.png

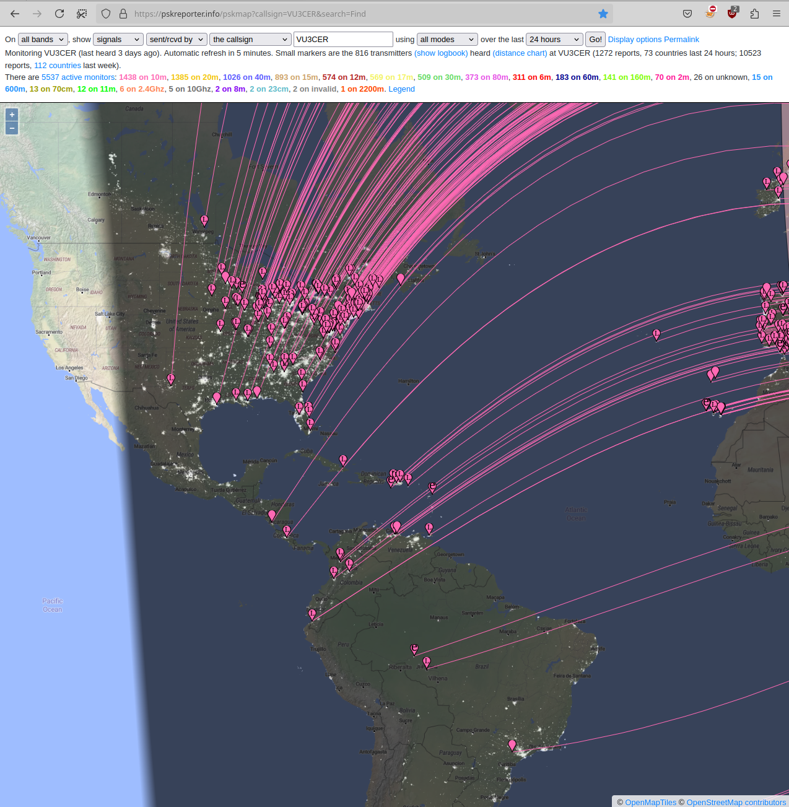
screenshots/Screenshot_2024-10-03_06-31-26.png
