kholia/DDX/screenshots/Screenshot_2024-10-04_07-43-27.png

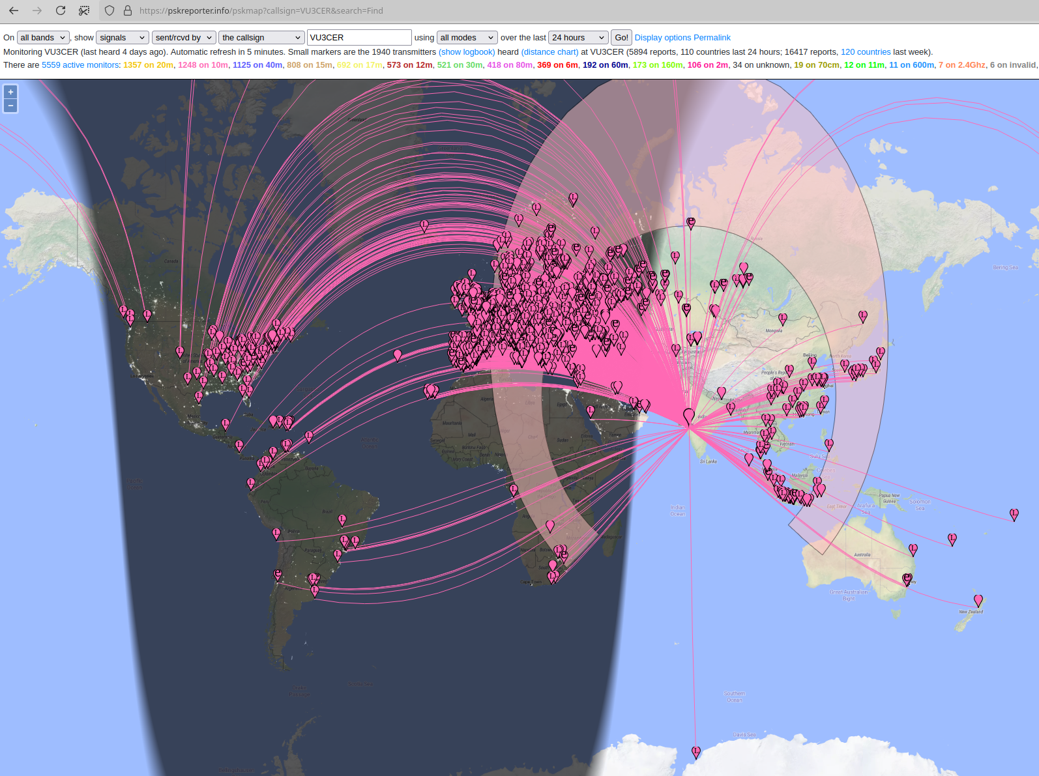
screenshots/Screenshot_2024-10-04_07-43-27.png
