kholia/DDX/screenshots/Screenshot_2024-10-05-10-07-06-128_com.bunzee.ft8radio.jpg

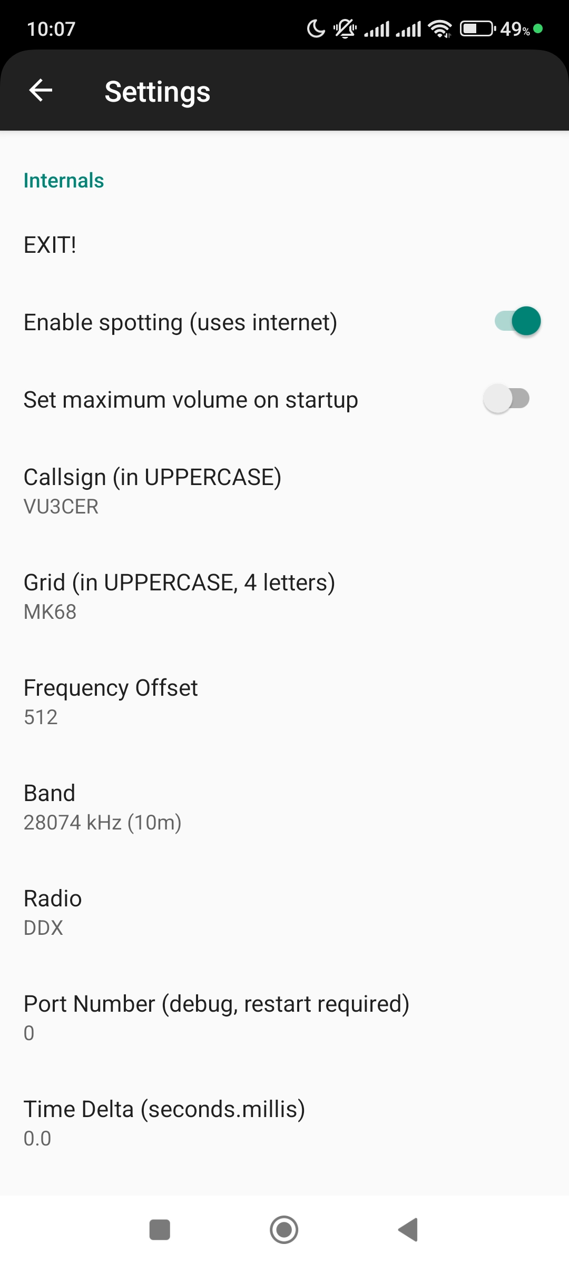
screenshots/Screenshot_2024-10-05-10-07-06-128_com.bunzee.ft8radio.jpg
