kholia/DDX/screenshots/Screenshot_2024-10-07_13-33-04.png

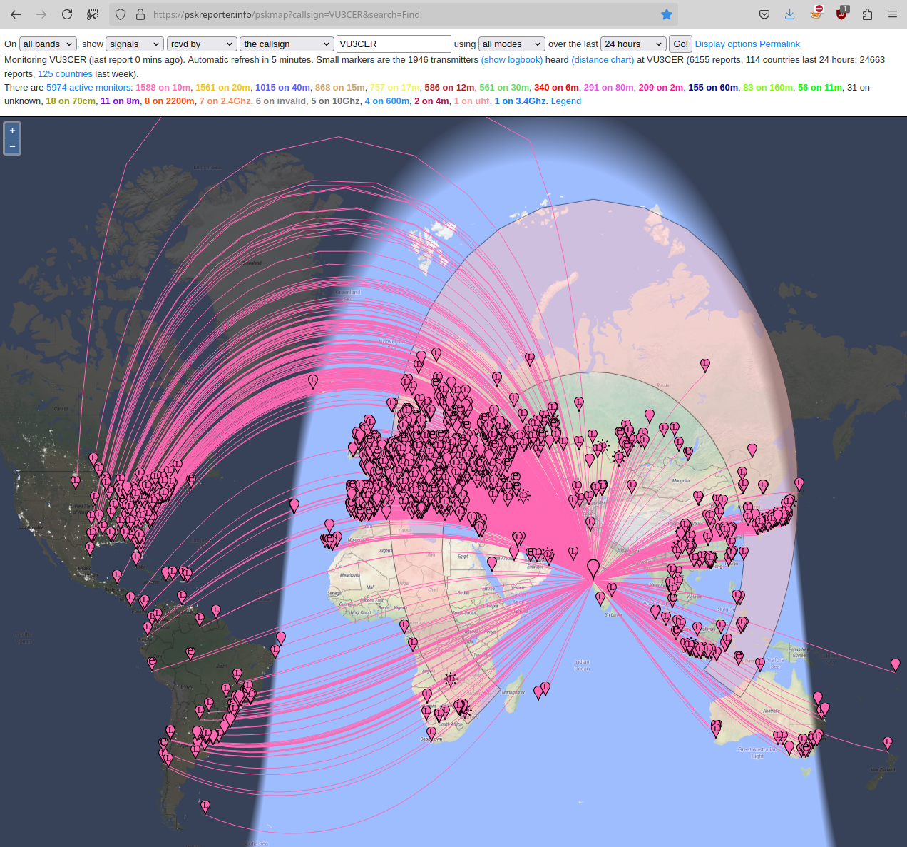
screenshots/Screenshot_2024-10-07_13-33-04.png
