kholia/DDX/screenshots/TX-Screenshot_2023-11-22_19-36-07.png

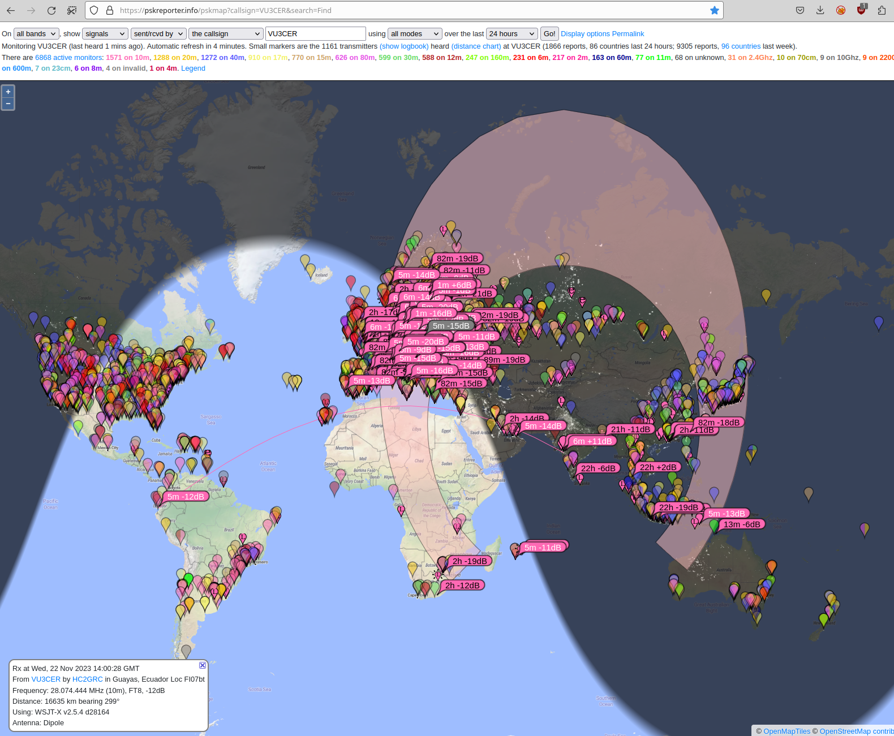
screenshots/TX-Screenshot_2023-11-22_19-36-07.png
