kholia/DDX/screenshots/TX-Spread-Screenshot_2023-12-23_14-40-04.png

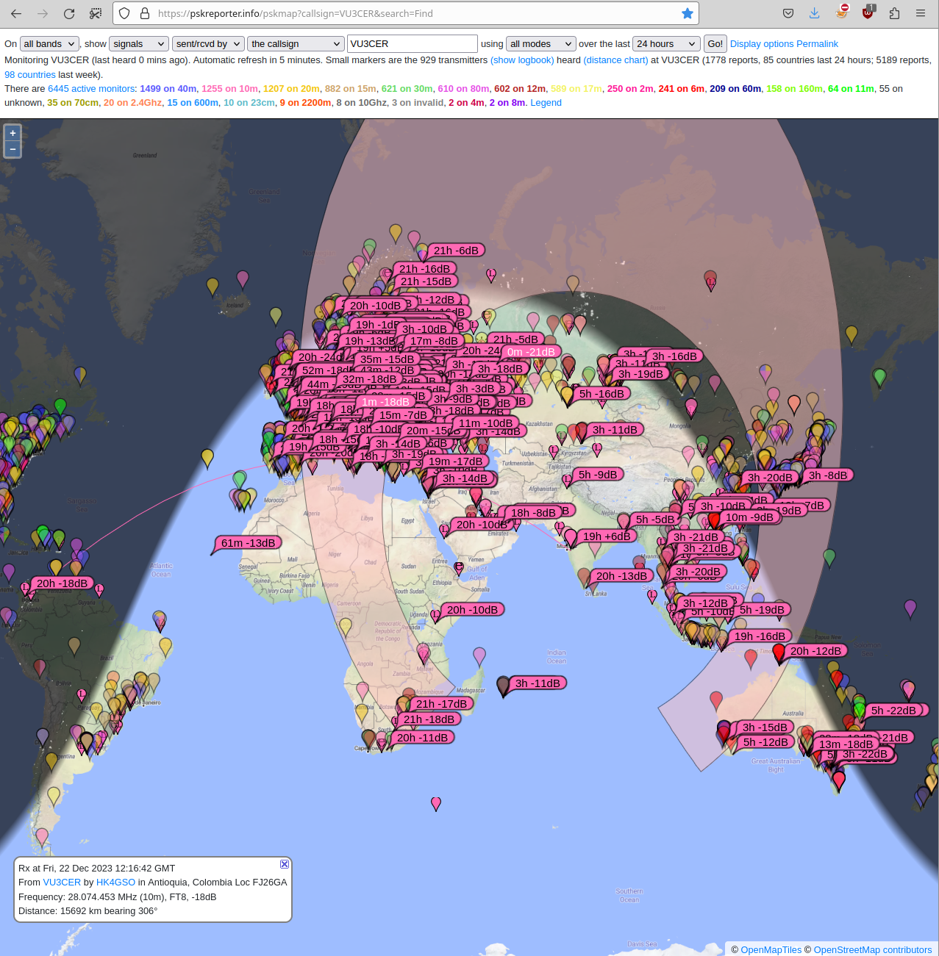
screenshots/TX-Spread-Screenshot_2023-12-23_14-40-04.png
