kholia/DDX/screenshots/US-Screenshot_2023-11-30_20-02-53.png

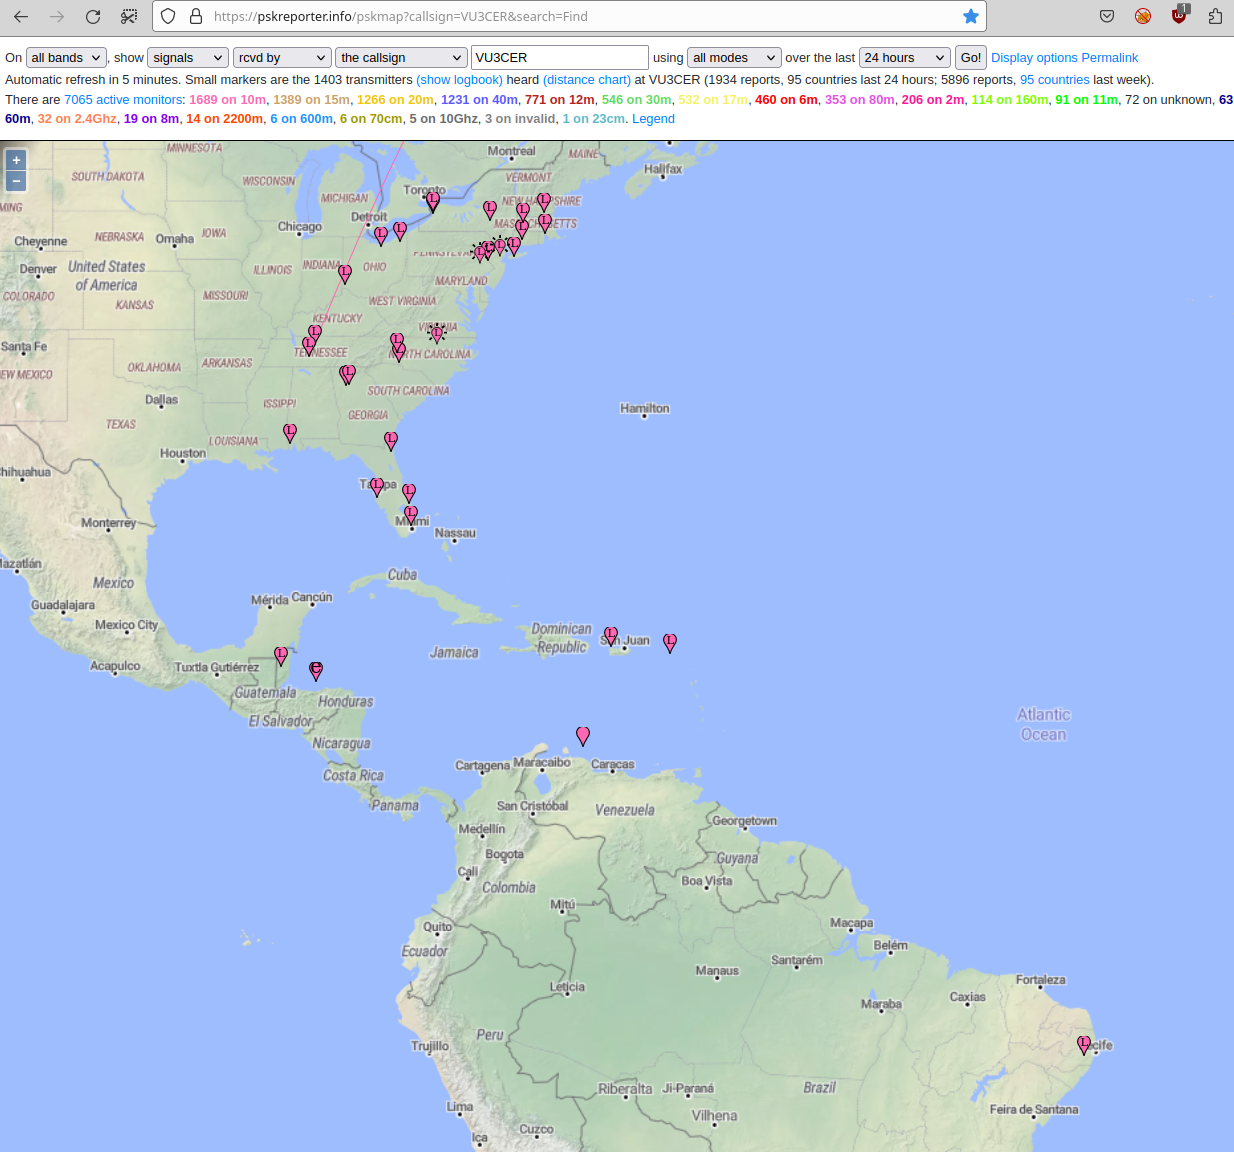
screenshots/US-Screenshot_2023-11-30_20-02-53.png
