kholia/DDX/screenshots/WP4U-QSO.png

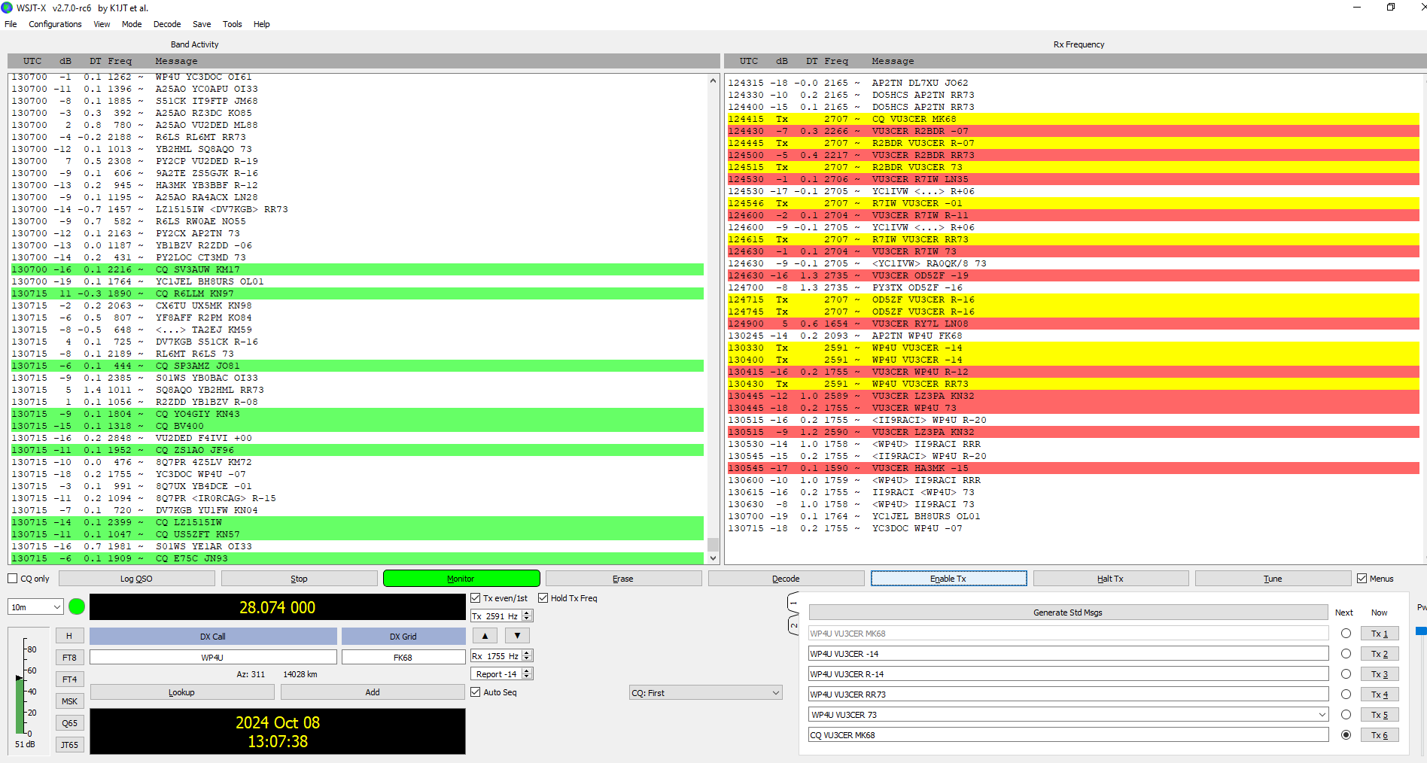
screenshots/WP4U-QSO.png
