kholia/DDX/screenshots/WSPR-RX-Breadboard/Screenshot_2023-11-24_17-04-43.png

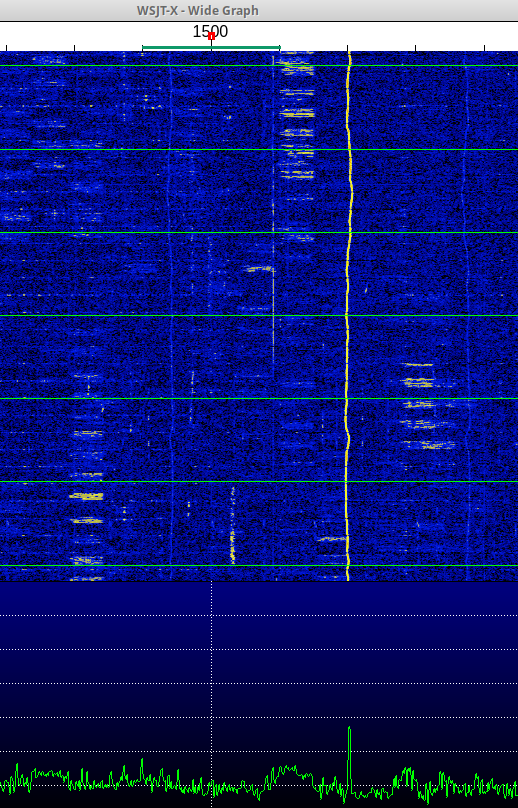
screenshots/WSPR-RX-Breadboard/Screenshot_2023-11-24_17-04-43.png
