kholia/DDX/RX-TX-BPF-2025-v2/models/Flat Inductor Coil 2.STEP

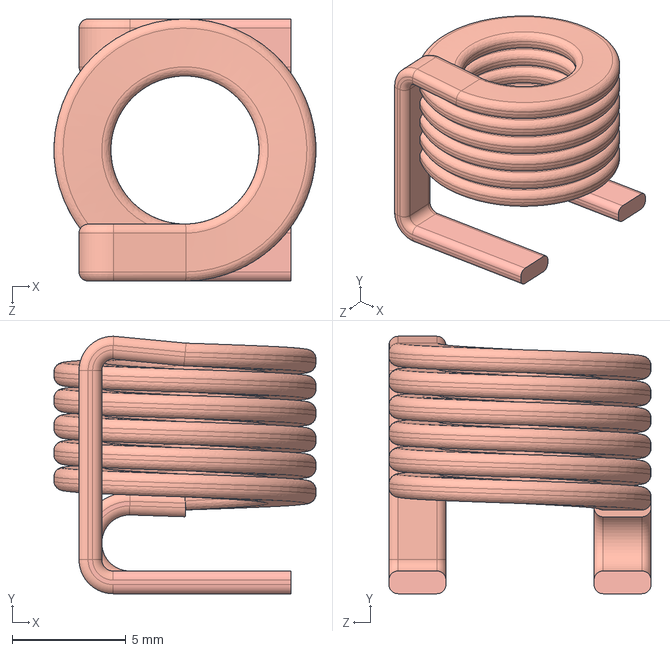
[picture p74: CAD file, 2024-12-21]
RX-TX-BPF-2025-v2/models/Flat Inductor Coil 2.STEP
11.5 x 11.3 x 11.5 mm
