kholia/DDX/Active-Antenna/models/raspberry pi pico.step

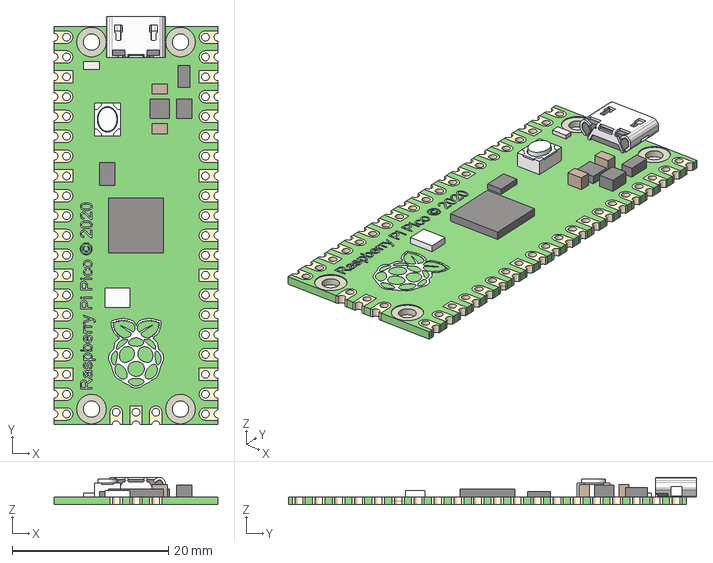
[picture p75: CAD file, 2024-12-24]
Active-Antenna/models/raspberry pi pico.step
21.0 x 52.3 x 3.50 mm
