kholia/DDX/Active-Antenna/models/SWPA8040S100MT.stp

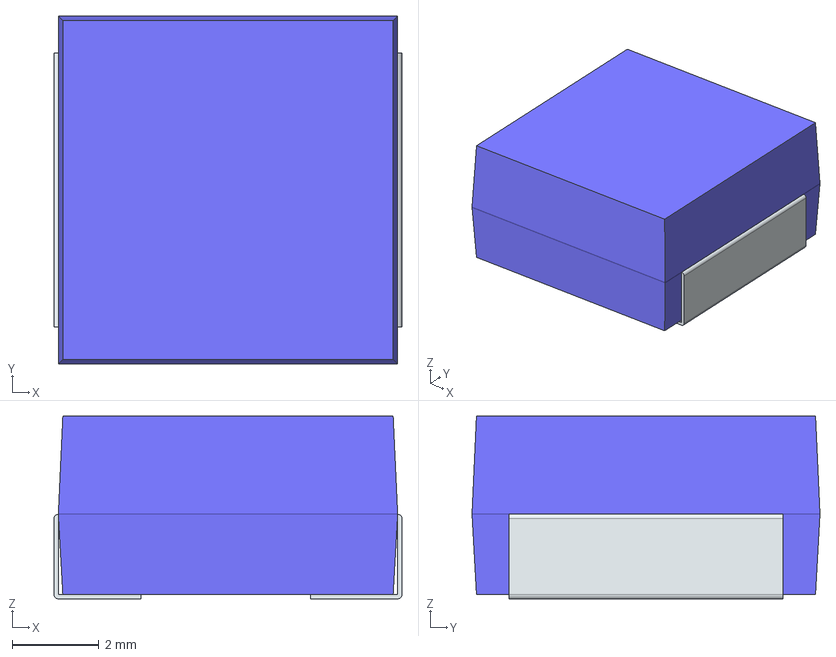
[picture p76: CAD file, 2024-12-24]
Active-Antenna/models/SWPA8040S100MT.stp
8.00 x 8.00 x 4.20 mm
FilletPin1
FilletPin2
