kholia/DDX/Active-Antenna/models/RELAY-SMD_L10.0-W6.5-H5.7-LS7.5-P2.2.step

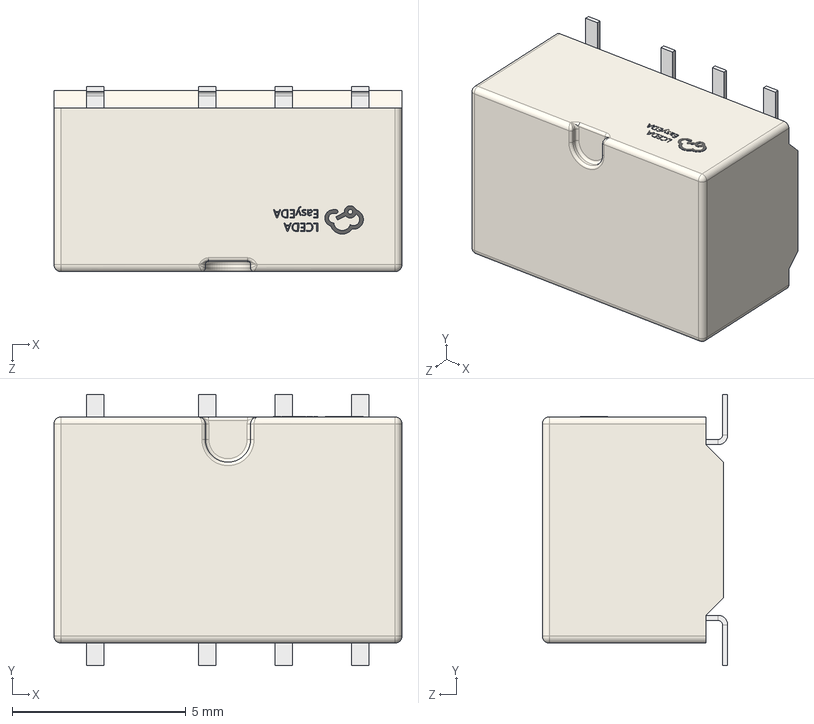
[picture p77: CAD file, 2024-12-24]
Active-Antenna/models/RELAY-SMD_L10.0-W6.5-H5.7-LS7.5-P2.2.step
10.0 x 7.80 x 5.33 mm
