kholia/DDX/Active-Antenna/models/RELAY-TH_HFD3-5.step

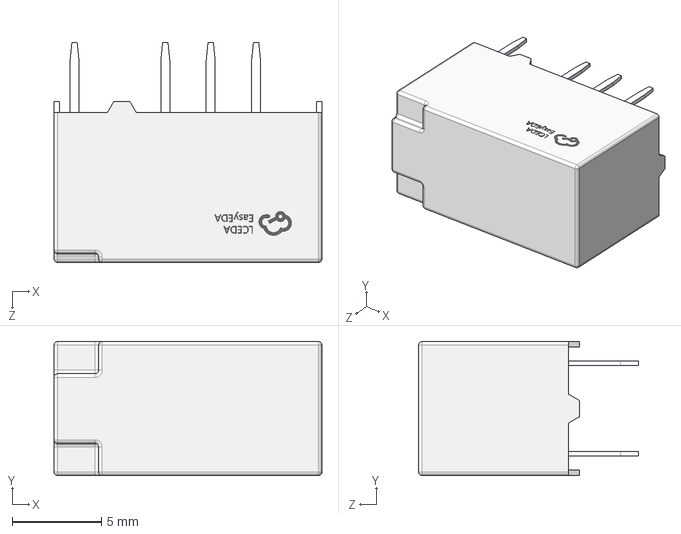
[picture p78: CAD file, 2024-12-24]
Active-Antenna/models/RELAY-TH_HFD3-5.step
15.0 x 7.51 x 12.3 mm
