kholia/DDX/Active-Antenna/models/raspberry pi pico with contacts.step

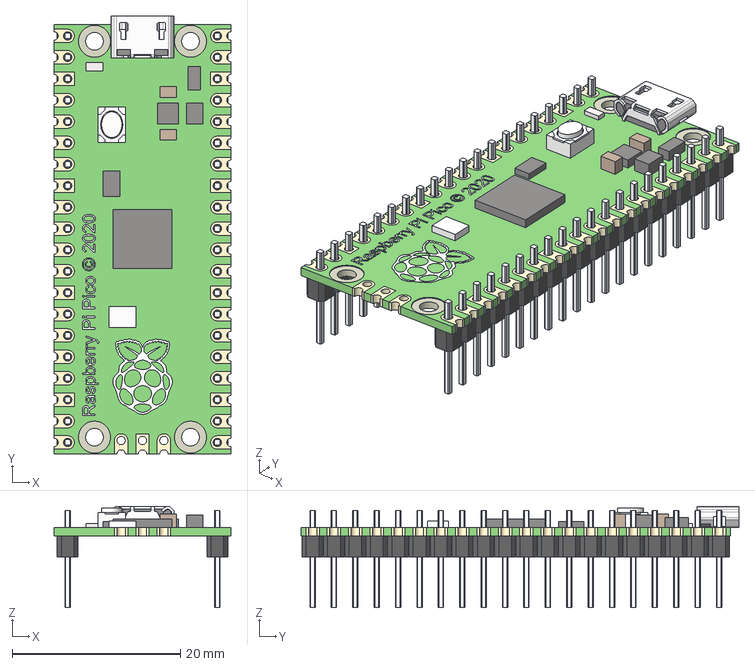
[picture p80: CAD file, 2024-12-24]
Active-Antenna/models/raspberry pi pico with contacts.step
21.0 x 52.0 x 12.0 mm
ножка x 20
ножка v3(Mirror) x 20
