kholia/DDX/Active-Antenna/models/Poti_10kohm.stp

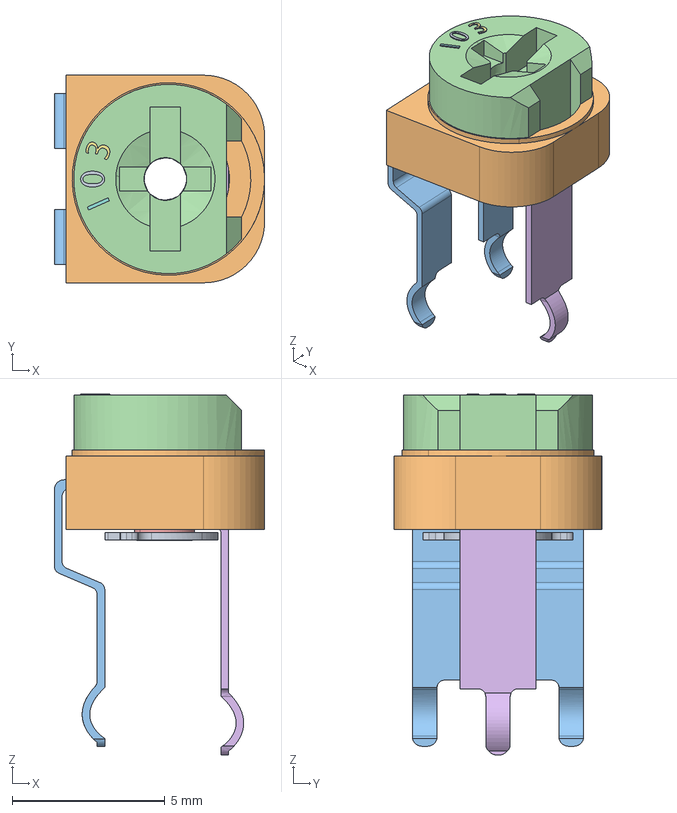
[picture p81: CAD file, 2024-07-30]
Active-Antenna/models/Poti_10kohm.stp
6.88 x 6.80 x 11.8 mm
