kholia/DDX/Active-Antenna/models/TO-220-3 Bend Mirror.stp

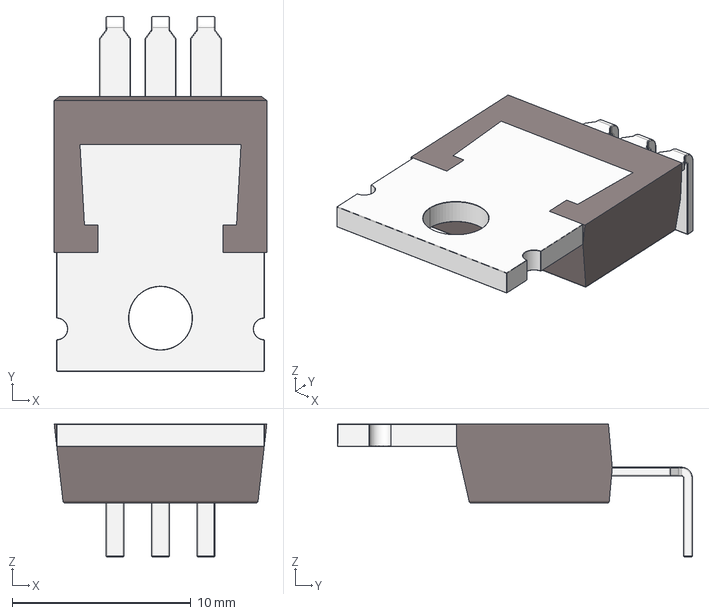
[picture p82: CAD file, 2024-07-30]
Active-Antenna/models/TO-220-3 Bend Mirror.stp
11.9 x 19.8 x 7.41 mm
