kholia/DDX/Active-Antenna/models/Toggle Switch 6 Pins-SPDT-ON-OFF-ON (6A,125VAC).STEP

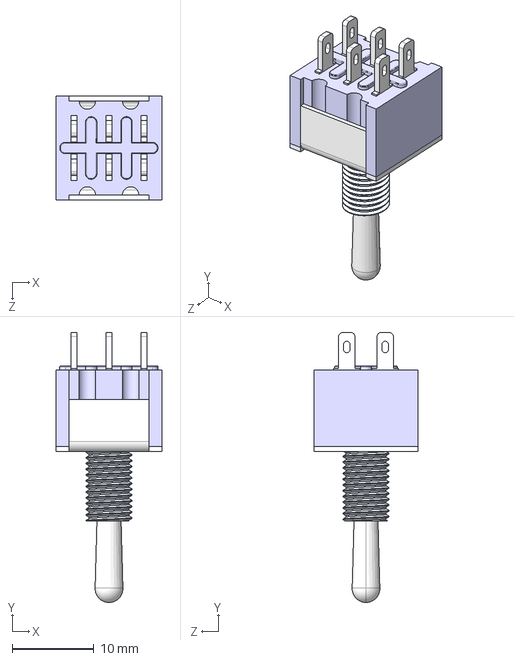
[picture p83: CAD file, 2024-07-30]
Active-Antenna/models/Toggle Switch 6 Pins-SPDT-ON-OFF-ON (6A,125VAC).STEP
13.0 x 33.0 x 12.7 mm
