kholia/DDX/Active-Antenna/models/DC-005-5A-2.0.step

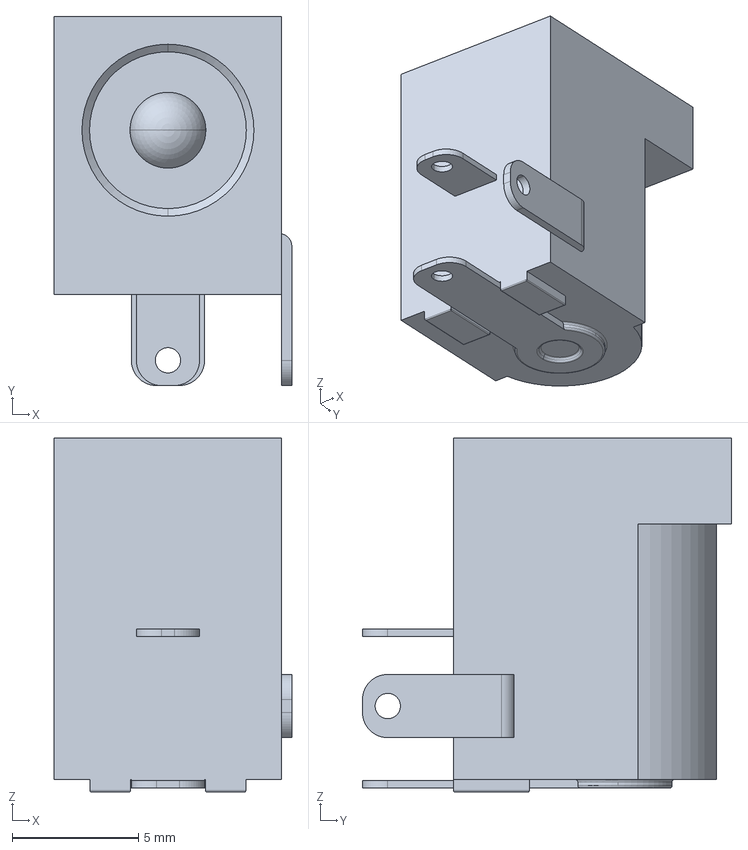
[picture p84: CAD file, 2024-05-13]
Active-Antenna/models/DC-005-5A-2.0.step
9.40 x 14.6 x 14.0 mm
