kholia/DDX/Active-Antenna/models/901-144.stp

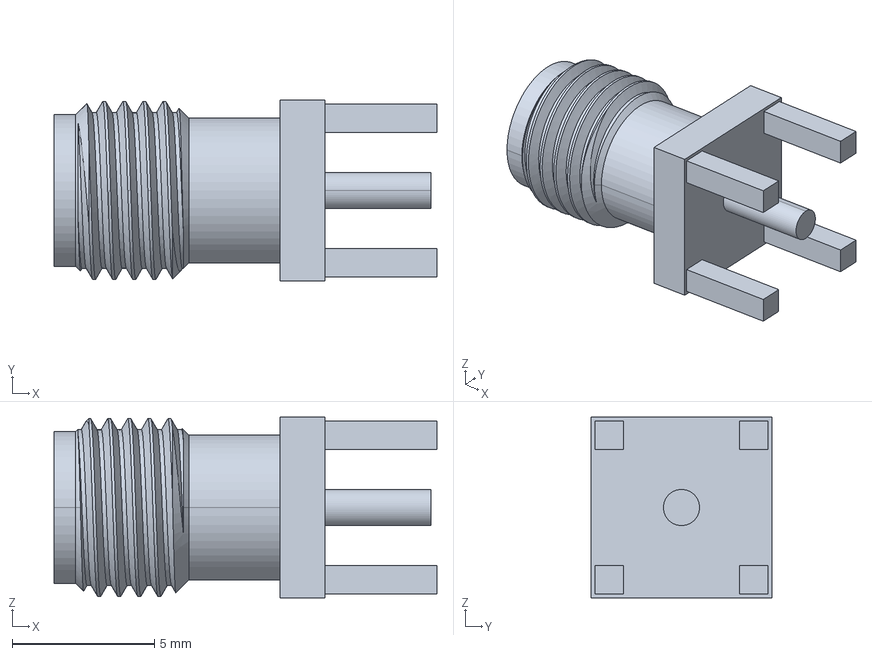
[picture p85: CAD file, 2024-05-13]
Active-Antenna/models/901-144.stp
13.5 x 6.35 x 6.35 mm
