kholia/DDX/Active-Antenna/models/BPF-1.step

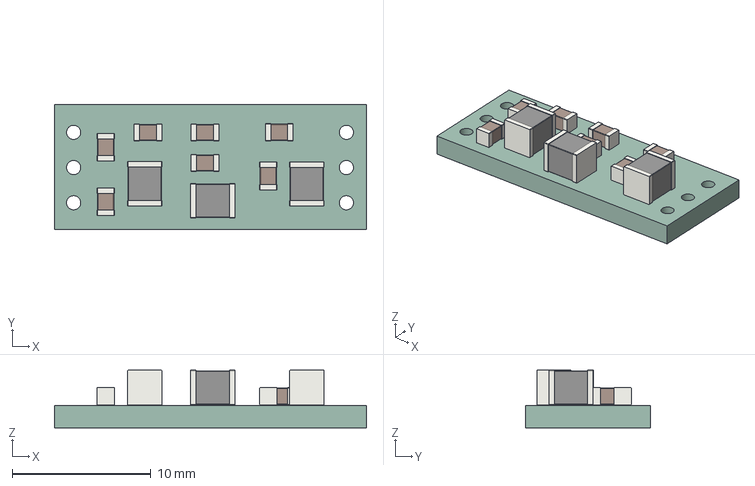
[picture p86: CAD file, 2024-05-13]
Active-Antenna/models/BPF-1.step
22.5 x 9.00 x 4.15 mm
Band_MODULE_V1_00 PCB
