kholia/DDX/Active-Antenna/models/SRR1260-4R7Y.stp

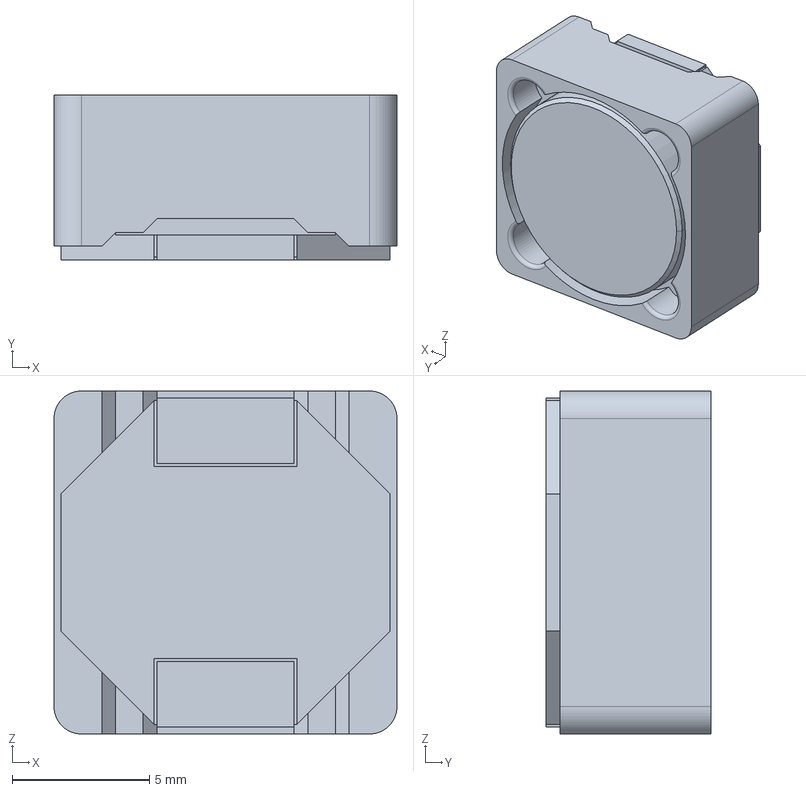
[picture p87: CAD file, 2024-05-13]
Active-Antenna/models/SRR1260-4R7Y.stp
12.5 x 6.00 x 12.5 mm
