kholia/DDX/Active-Antenna/models/Transistor_TO-92_Type.STEP

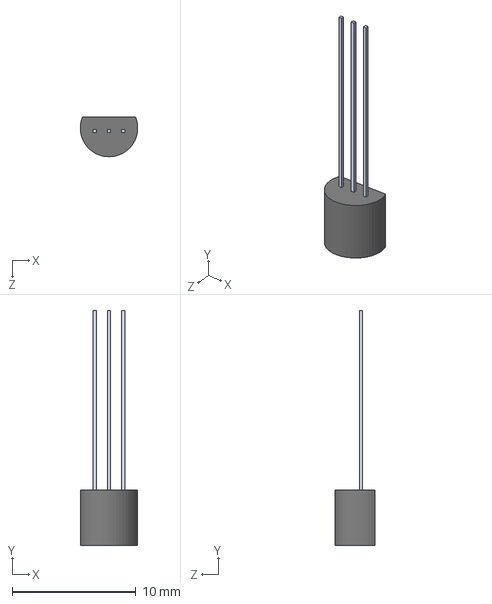
[picture p88: CAD file, 2024-05-13]
Active-Antenna/models/Transistor_TO-92_Type.STEP
4.64 x 19.0 x 3.20 mm
