kholia/DDX/Active-Antenna/models/Adafruit Si5351A.step

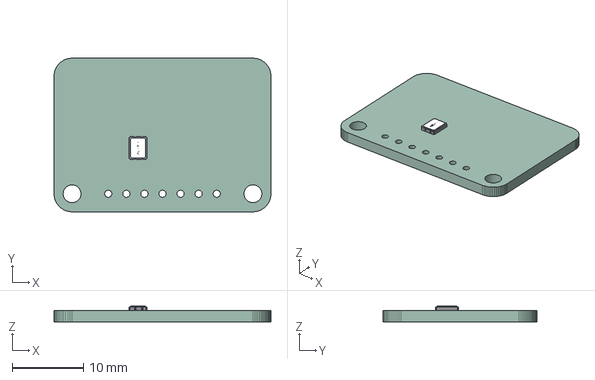
[picture p89: CAD file, 2024-05-13]
Active-Antenna/models/Adafruit Si5351A.step
30.5 x 21.6 x 2.20 mm
PCB
