kholia/DDX/Active-Antenna/models/5019.STEP

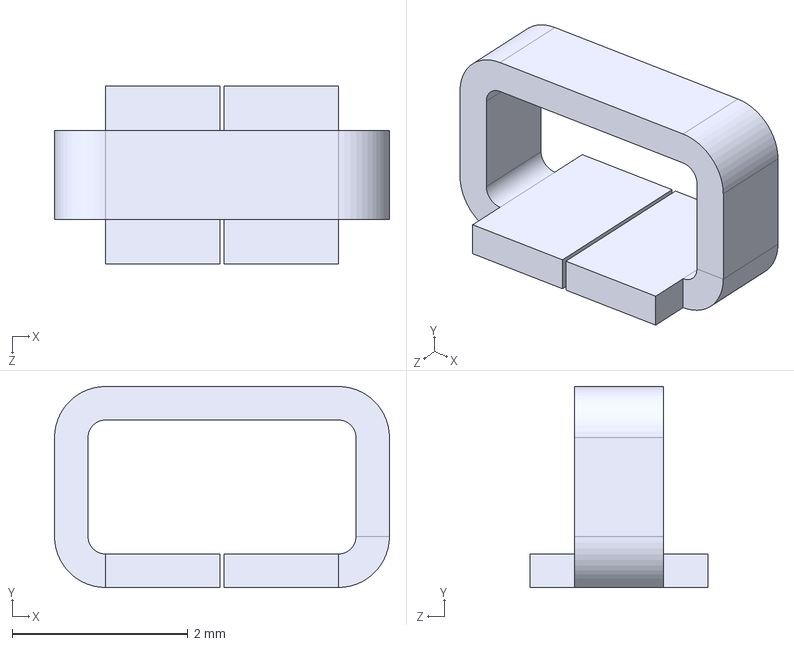
[picture p90: CAD file, 2024-05-13]
Active-Antenna/models/5019.STEP
3.81 x 2.29 x 2.03 mm
