kholia/DDX/Active-Antenna/models/ASPI-0630LR-4R7M-T15.step

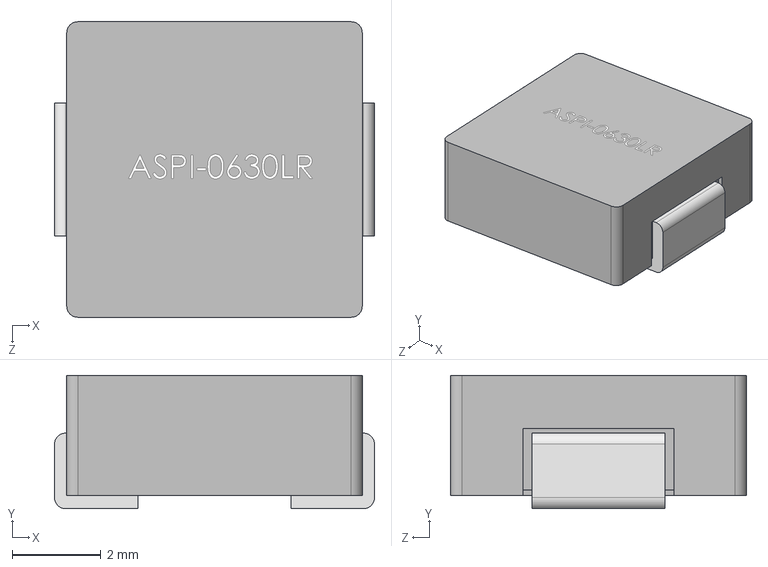
[picture p91: CAD file, 2024-05-13]
Active-Antenna/models/ASPI-0630LR-4R7M-T15.step
7.20 x 3.00 x 6.65 mm
