kholia/DDX/Active-Antenna/models/3314j-1-501e.stp

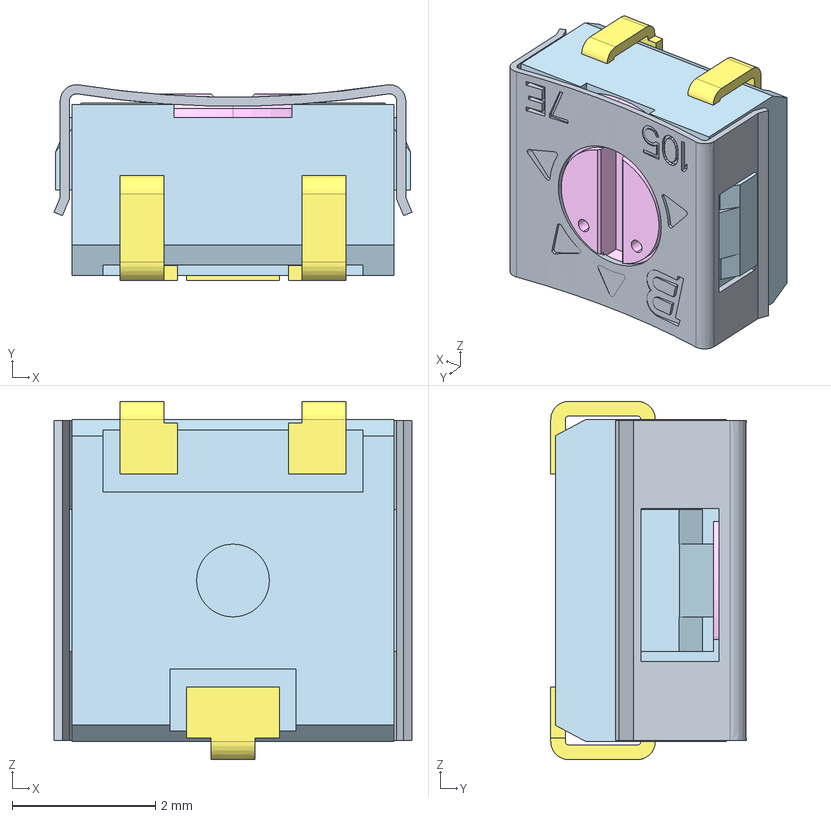
[picture p92: CAD file, 2024-05-13]
Active-Antenna/models/3314j-1-501e.stp
5.00 x 2.73 x 5.00 mm
