kholia/DDX/Active-Antenna/models/CON-SMA-EDGE-S--3DModel-STEP-56544.STEP

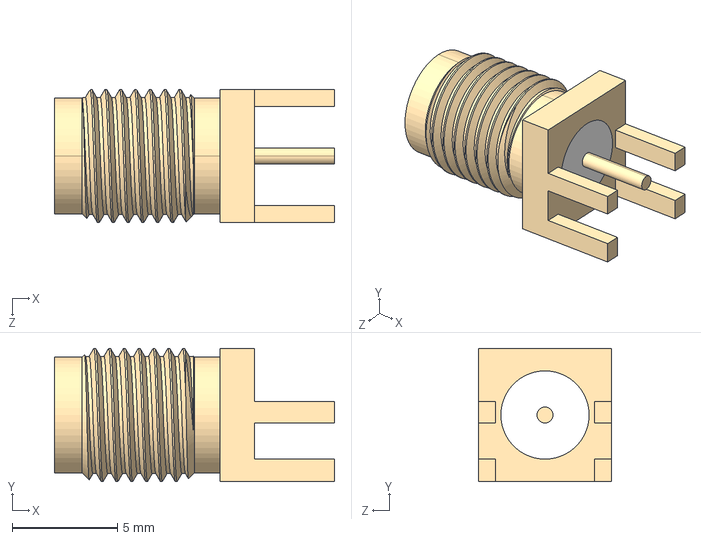
[picture p93: CAD file, 2024-05-13]
Active-Antenna/models/CON-SMA-EDGE-S--3DModel-STEP-56544.STEP
13.3 x 6.35 x 6.35 mm
