kholia/DDX/Active-Antenna/models/pj-307.step

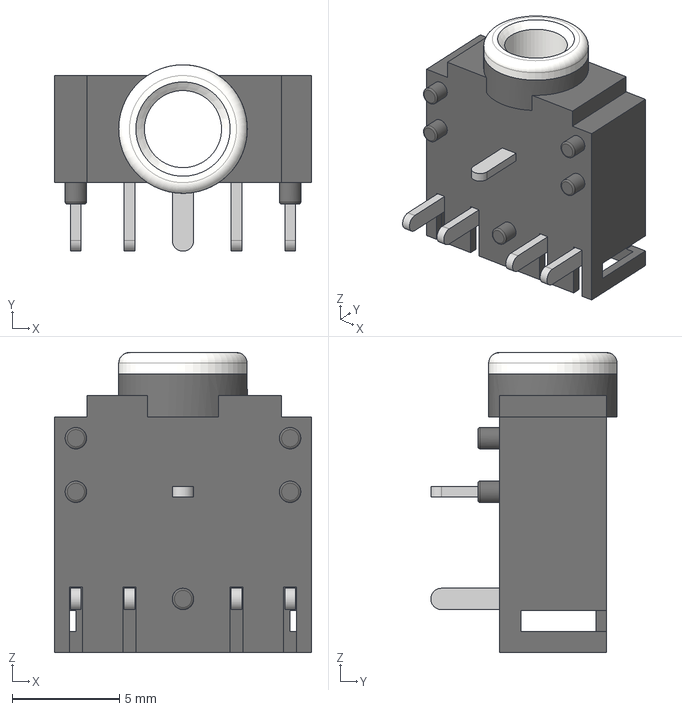
[picture p95: CAD file, 2024-05-13]
Active-Antenna/models/pj-307.step
12.0 x 8.70 x 14.0 mm
