kholia/DDX/Active-Antenna/models/TO_I510G_VIS.step

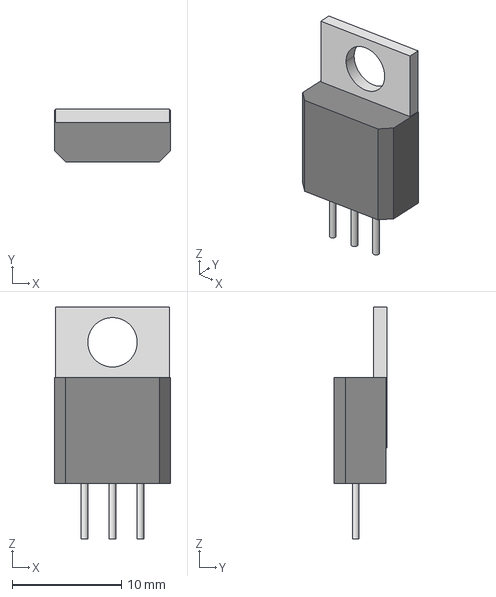
[picture p96: CAD file, 2024-05-13]
Active-Antenna/models/TO_I510G_VIS.step
10.6 x 4.83 x 21.2 mm
