kholia/DDX/Active-Antenna/models/pcb_connector_316-87-103-41-006101.stp

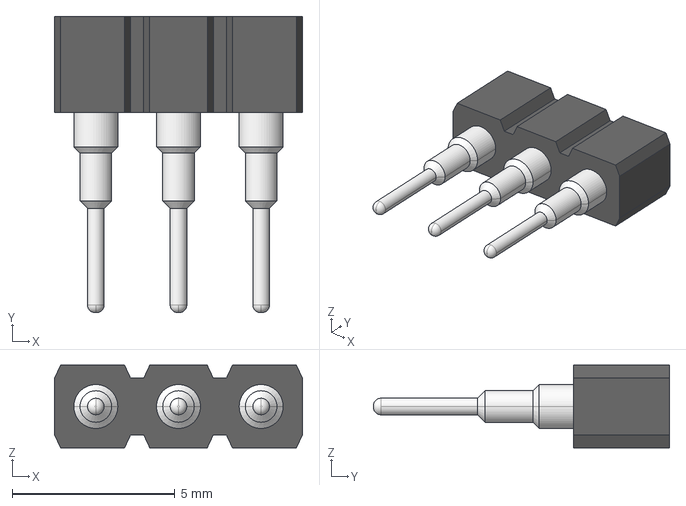
[picture p97: CAD file, 2024-05-13]
Active-Antenna/models/pcb_connector_316-87-103-41-006101.stp
7.62 x 9.10 x 2.54 mm
