kholia/DDX/Active-Antenna/models/22-23-2021.stp

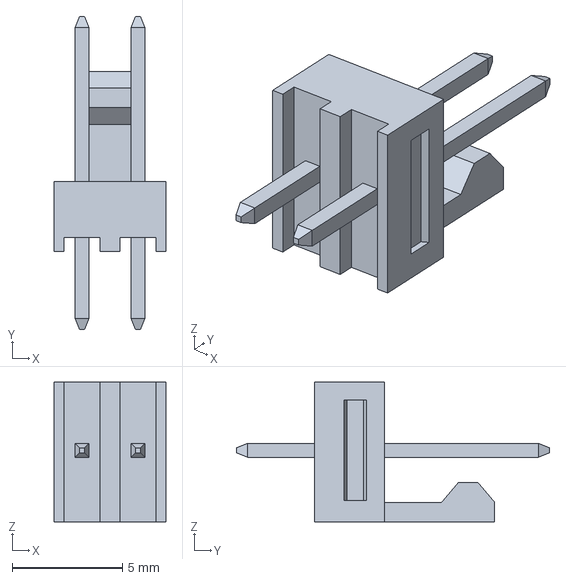
[picture p98: CAD file, 2024-05-13]
Active-Antenna/models/22-23-2021.stp
5.08 x 14.2 x 6.35 mm
