kholia/DDX/Active-Antenna/models/BoB.step

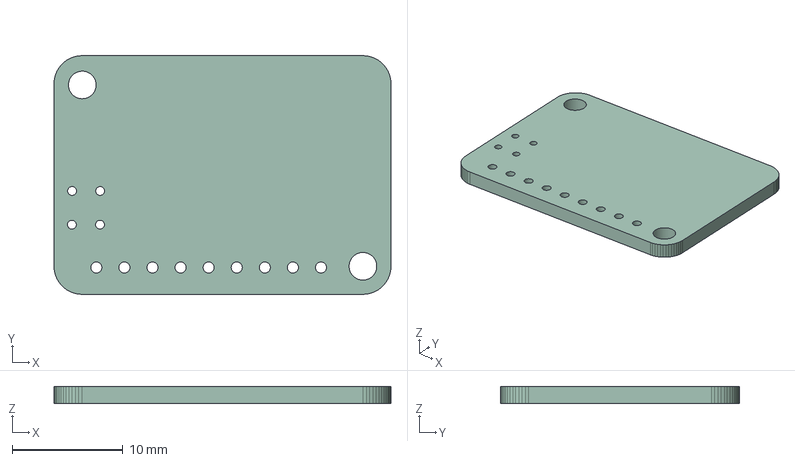
[picture p99: CAD file, 2024-05-13]
Active-Antenna/models/BoB.step
30.5 x 21.6 x 1.58 mm
