kholia/DDX/Active-Antenna/models/smd1812.stp

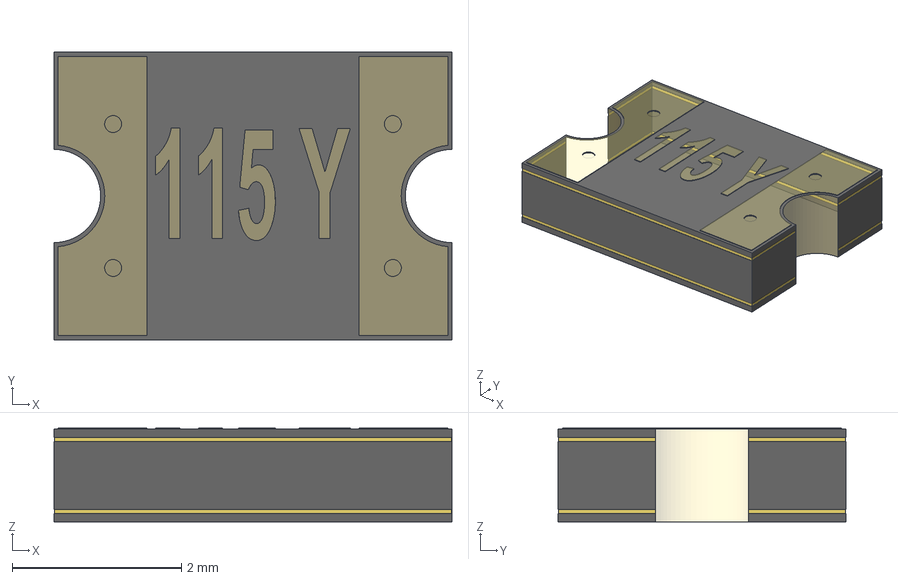
[picture p100: CAD file, 2024-05-13]
Active-Antenna/models/smd1812.stp
4.70 x 3.40 x 1.11 mm
