kholia/DDX/Active-Antenna/models/User Library-OMRON G5V-2.STEP

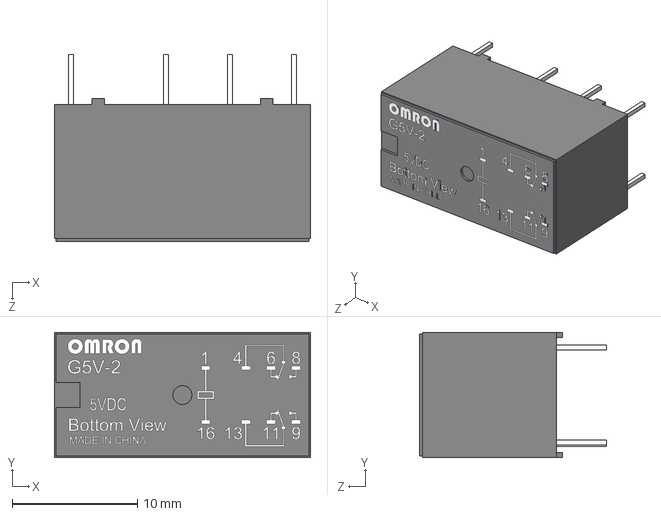
[picture p101: CAD file, 2024-05-13]
Active-Antenna/models/User Library-OMRON G5V-2.STEP
20.4 x 10.0 x 14.9 mm
