kholia/DDX/Active-Antenna/AA.pdf

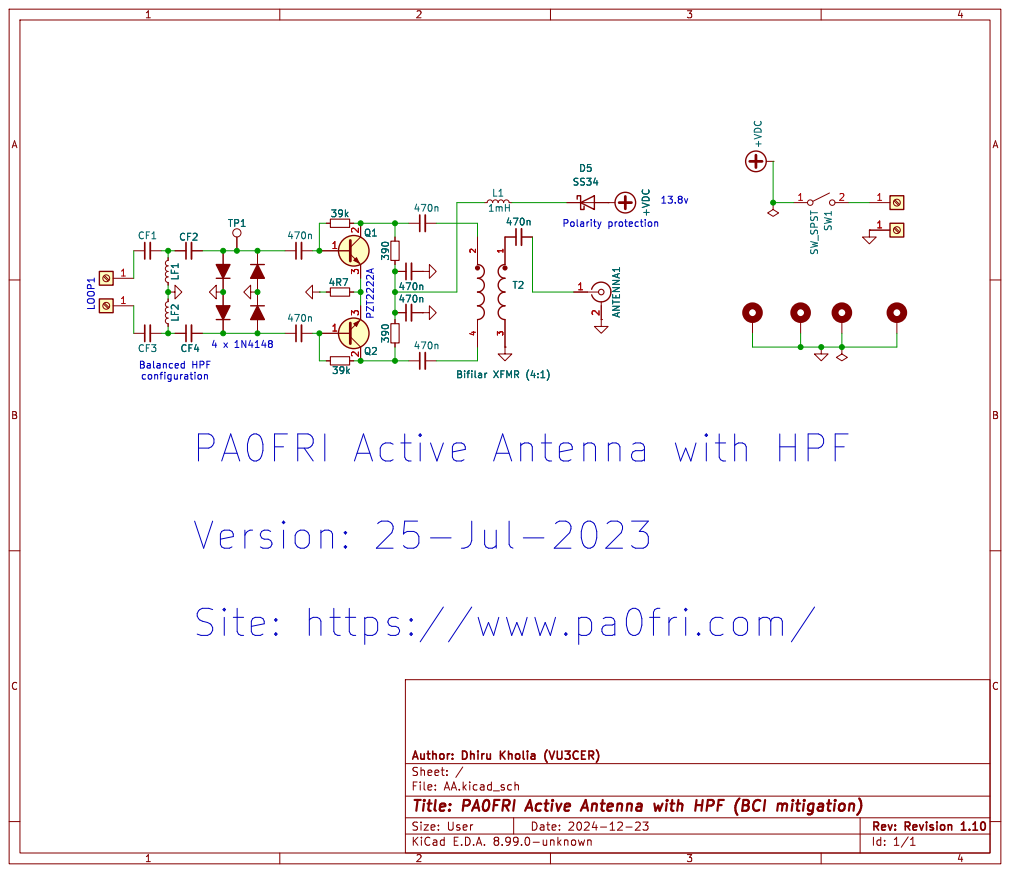
[picture p111: page 1]

Site: https://www.pa0fri.com/
